FLRHW/Strobe_main/HTML/images/cat_pdf_drill_map_Strobe_main-NPTH_drill_map.png

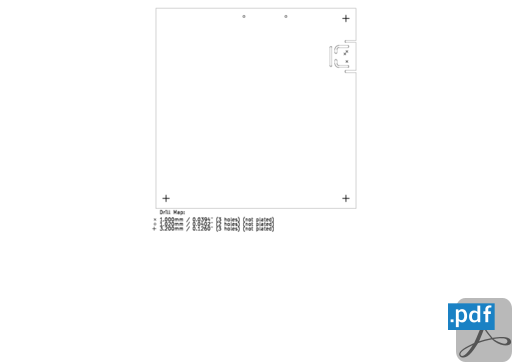
HTML/images/cat_pdf_drill_map_Strobe_main-NPTH_drill_map.png
