FLRHW/Strobe_main/HTML/images/cat_png_3d_viewer_bottom_Strobe_main-bottom.png

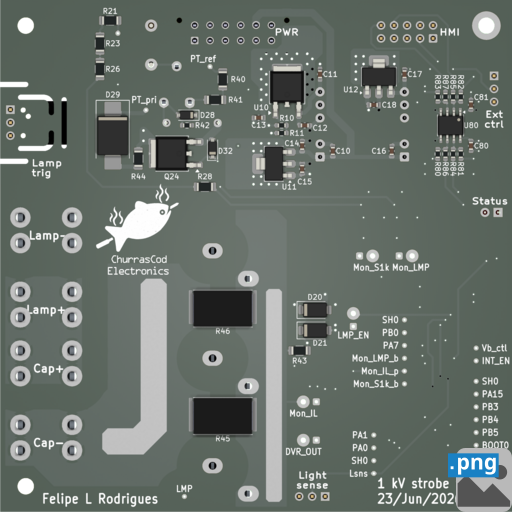
HTML/images/cat_png_3d_viewer_bottom_Strobe_main-bottom.png
