FLRHW/Strobe_main/HTML/images/cat_png_3d_viewer_top_Strobe_main-top.png

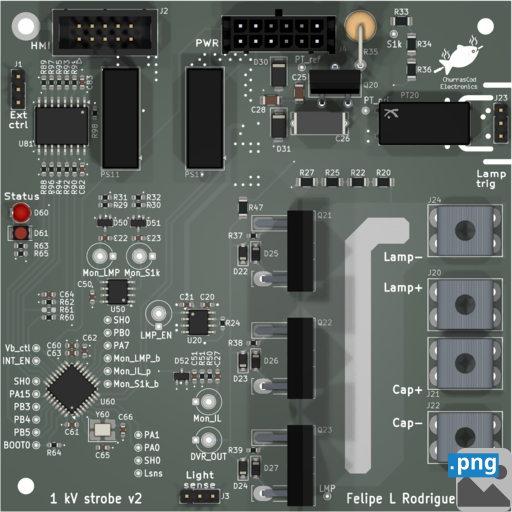
HTML/images/cat_png_3d_viewer_top_Strobe_main-top.png
