FLRHW/Strobe_main/Images/bot.jpg

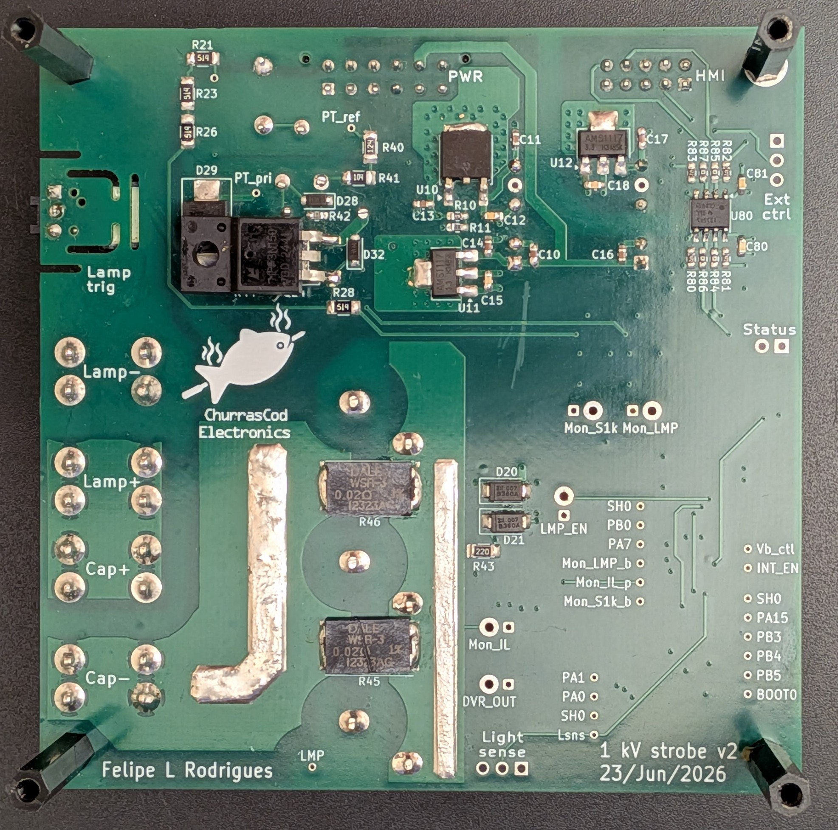
Images/bot.jpg
