FLRHW/Strobe_main/Manufacturing/Fabrication/Strobe_main-fabrication.pdf

# Top Fabrication (Scale 1:1) Main board Fabrication Document

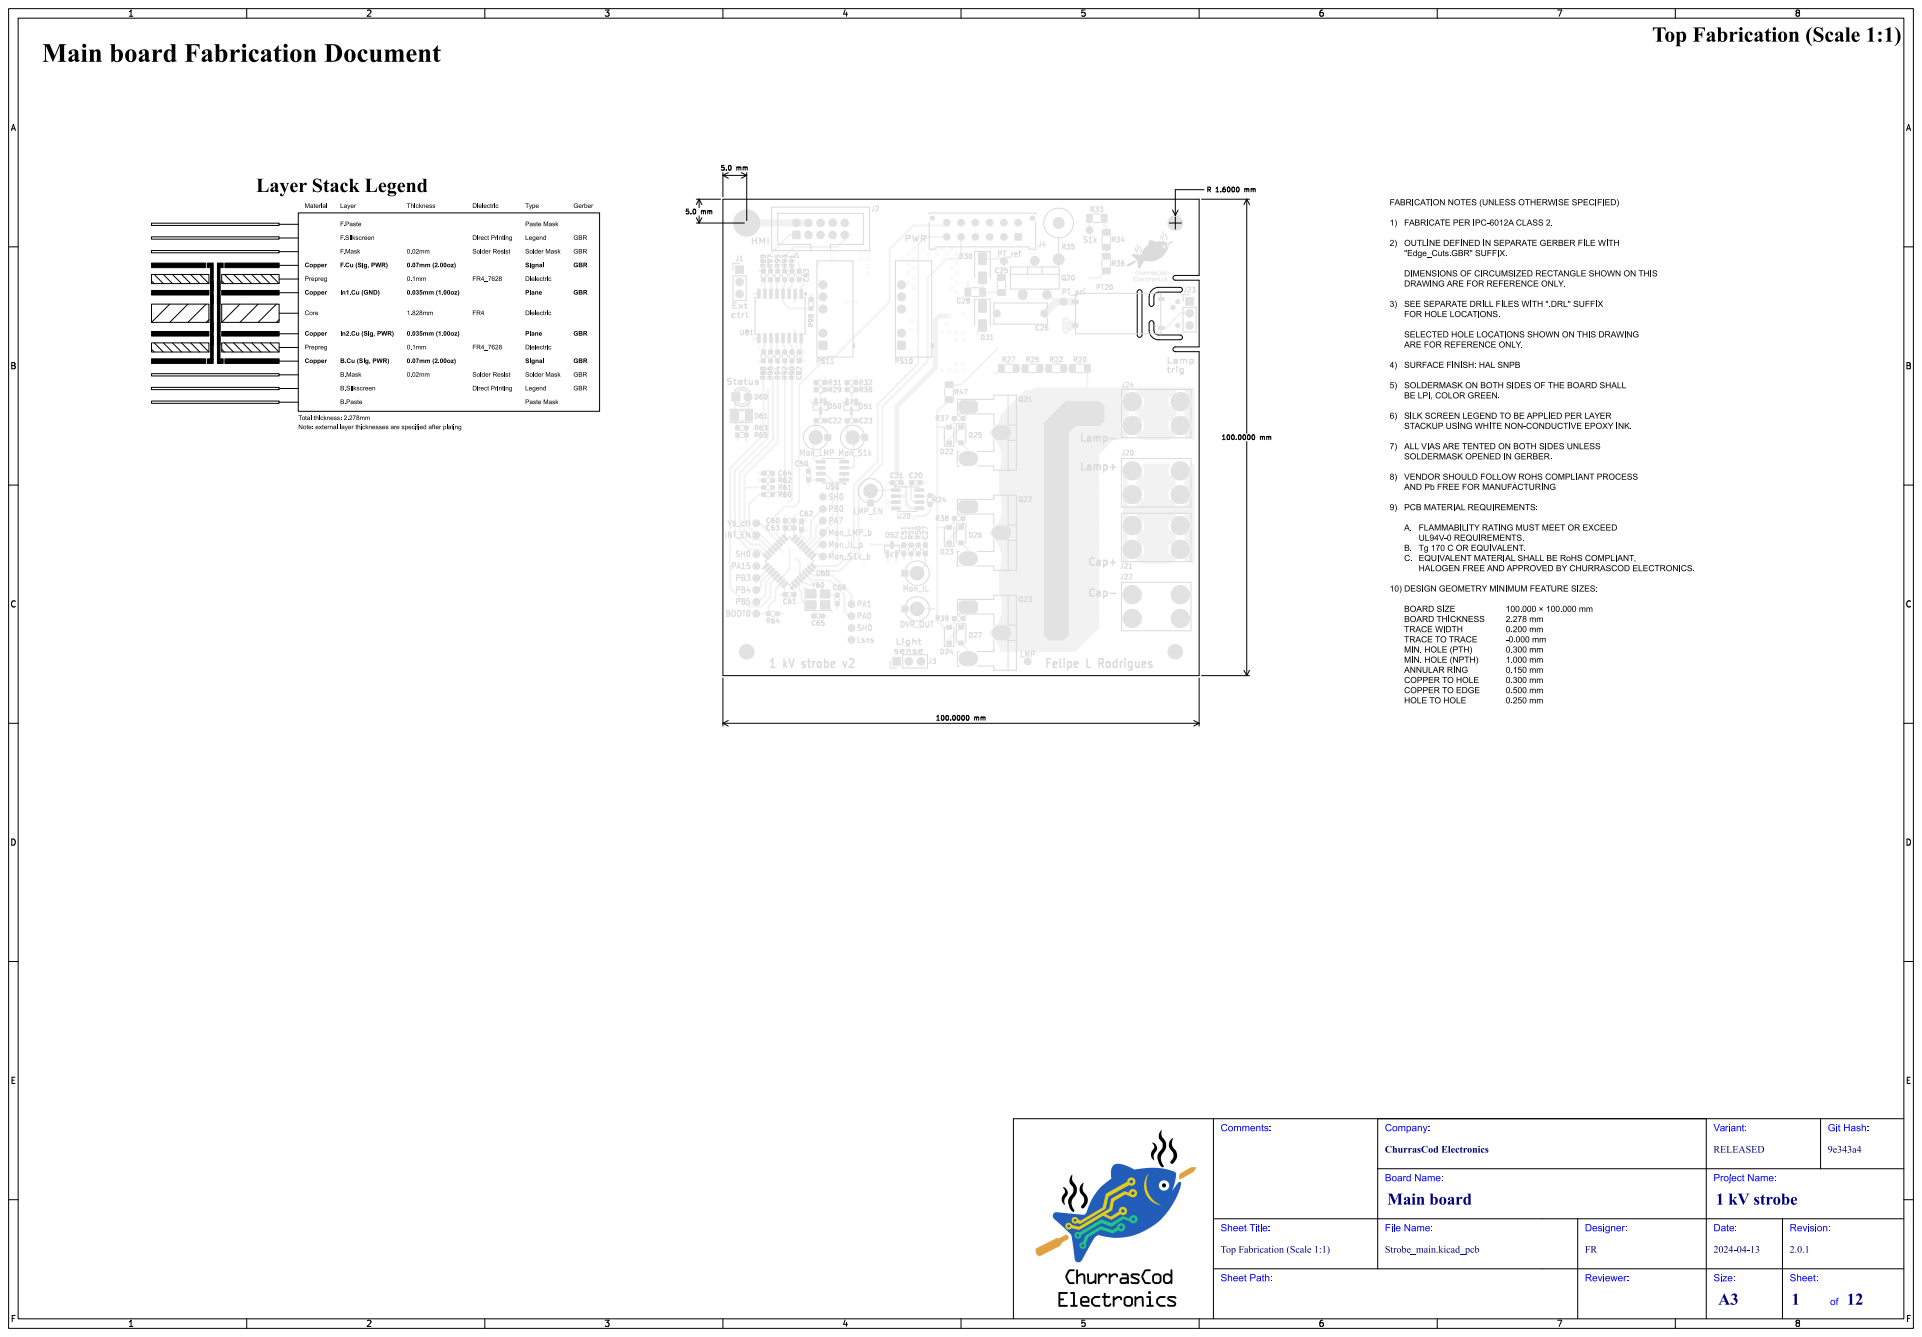
[picture p12: page 1]

# Bottom Fabrication (Scale 1:1) Main board Fabrication Document

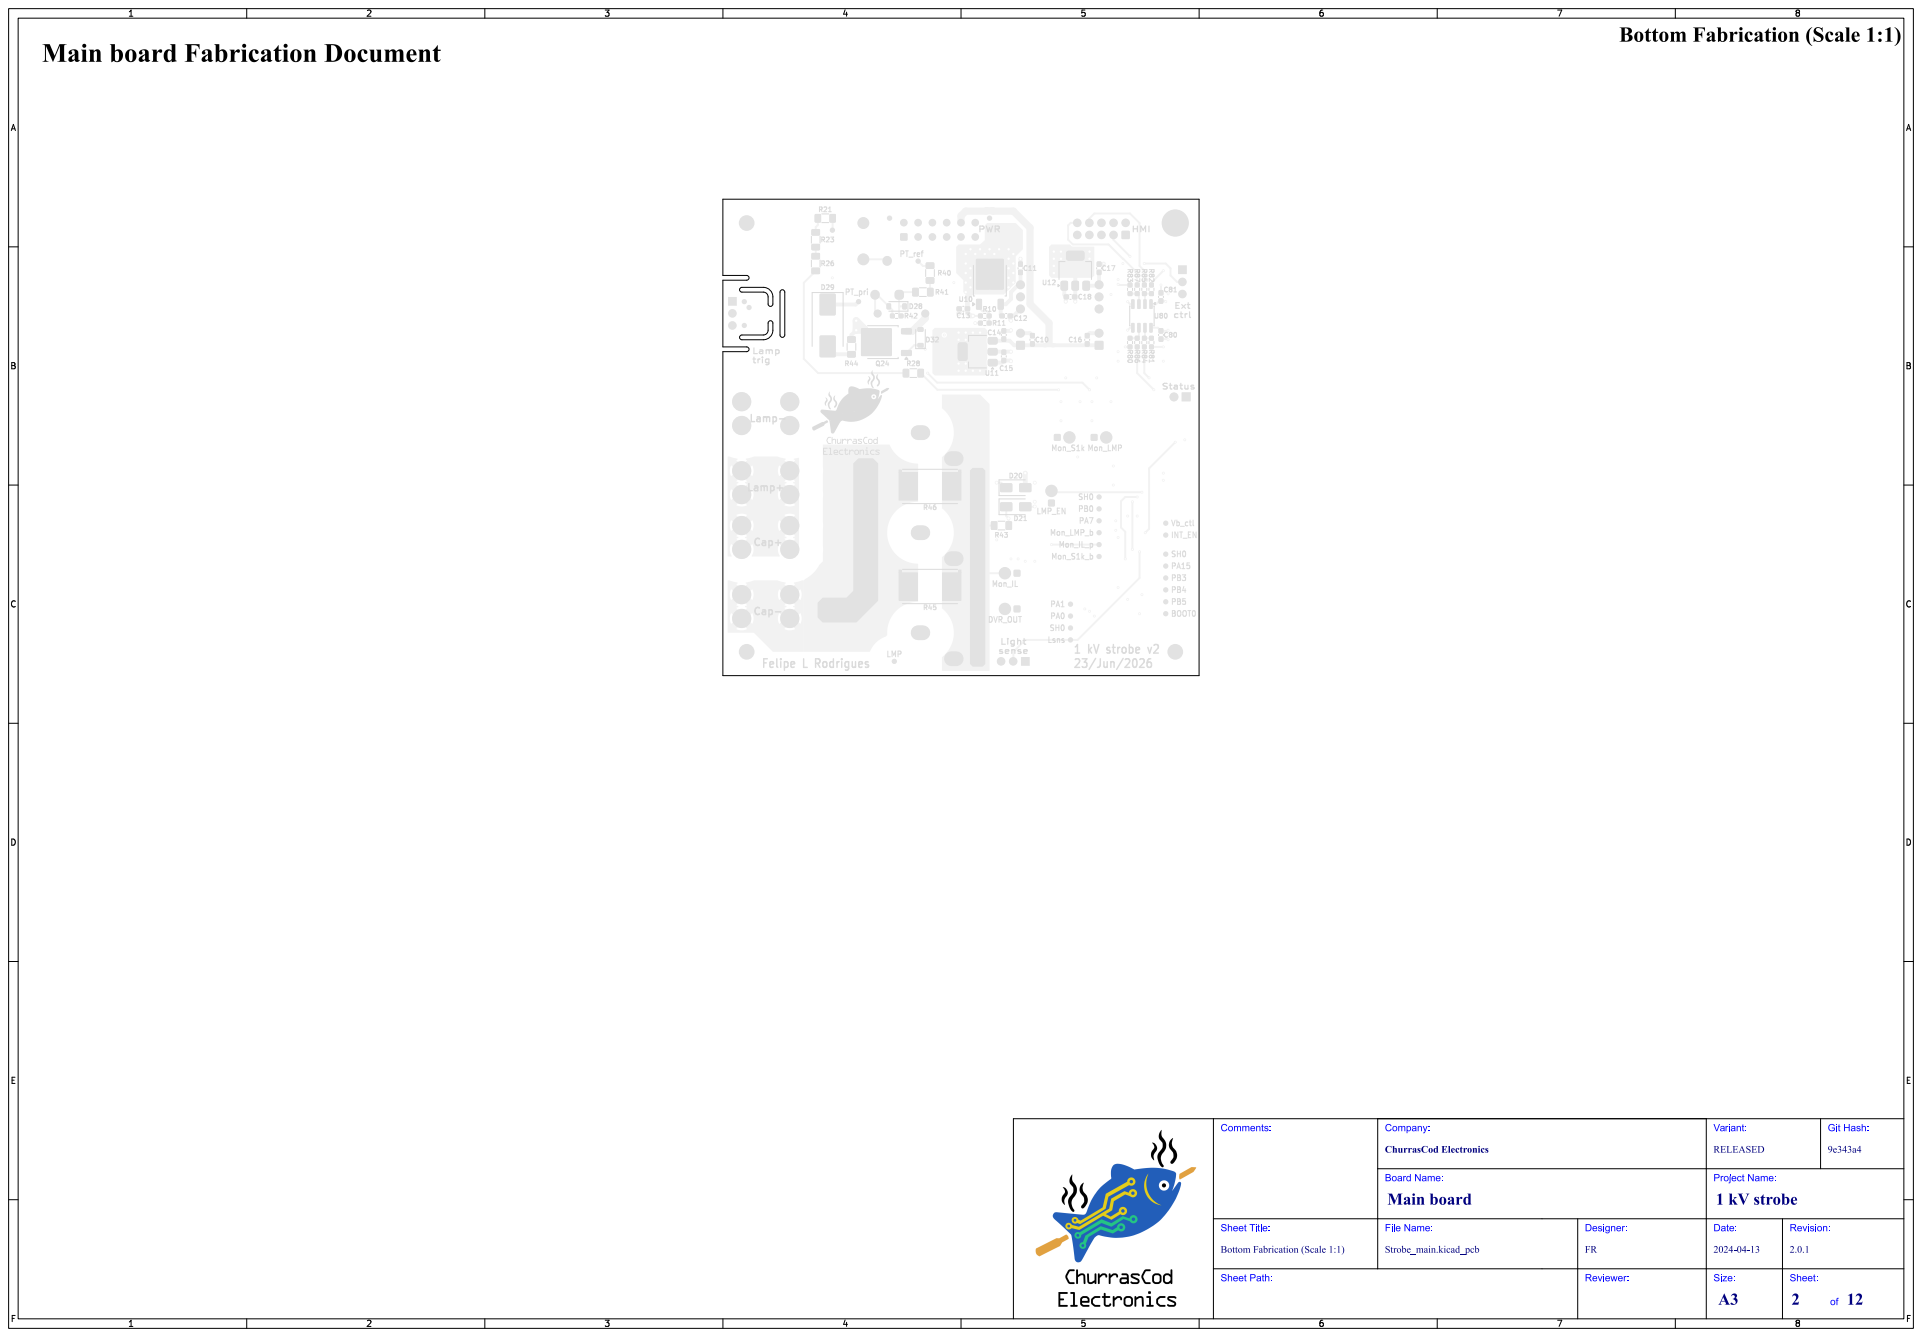
[picture p13: page 2]

# Drill Drawing L1 - L4 (Scale 1:1) Main board Fabrication Document

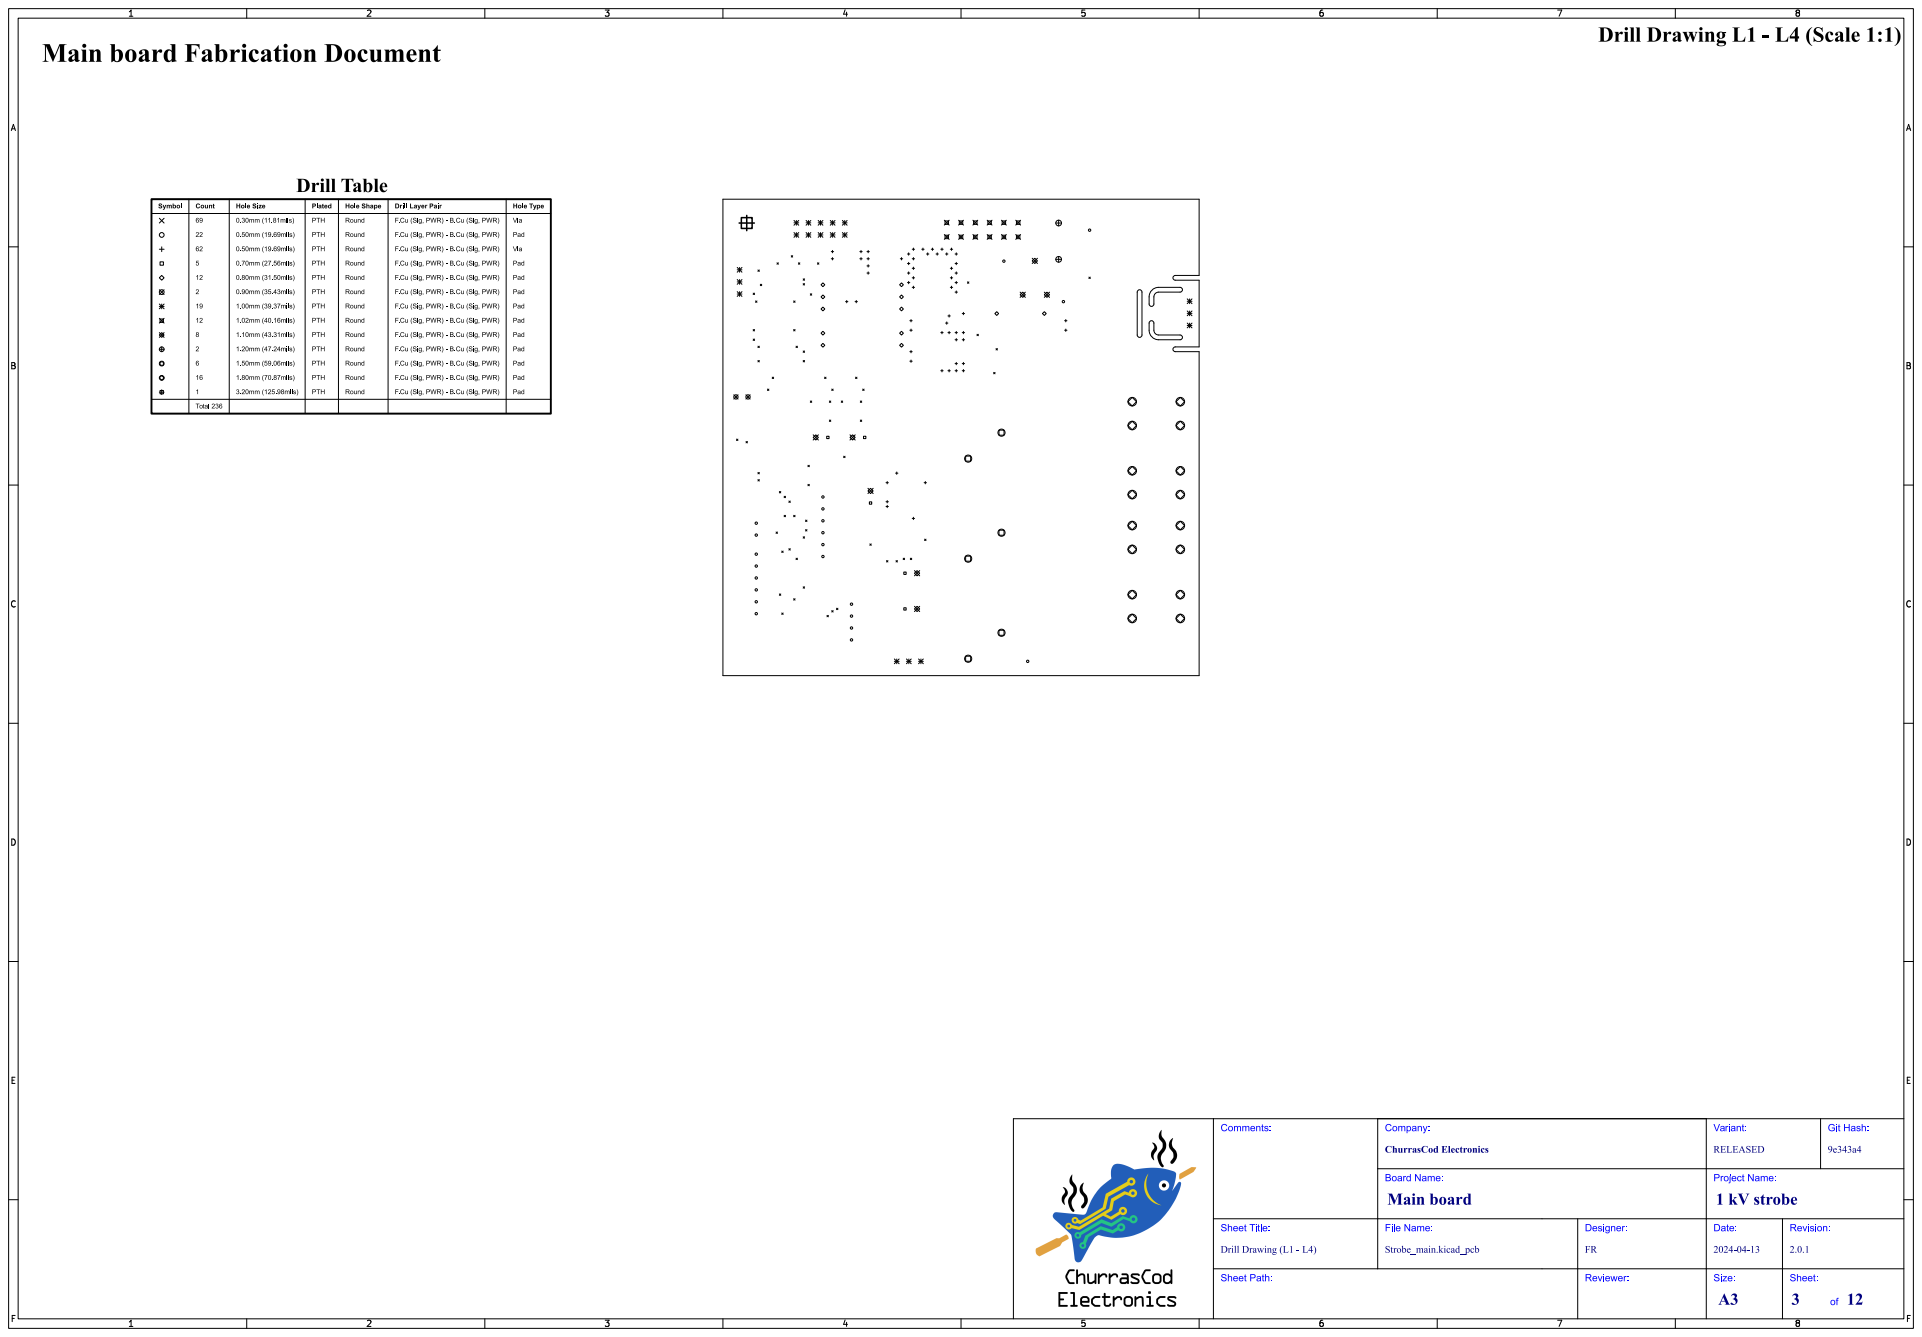
[picture p14: page 3]
Git; Hash:; Comments:; Drill Drawing (L1 - L4); Sheet Title:; File Name:; Main board; 1 kV strobe; ChurrasCod Electronics; Company:; RELEASED; Variant:; Board Name:; Strobe_main.kicad_pcb; Designer:; Project Name:; Date:; Revision:

# Drill Drawing L1 - L4 (Scale 1:1) Main board Fabrication Document

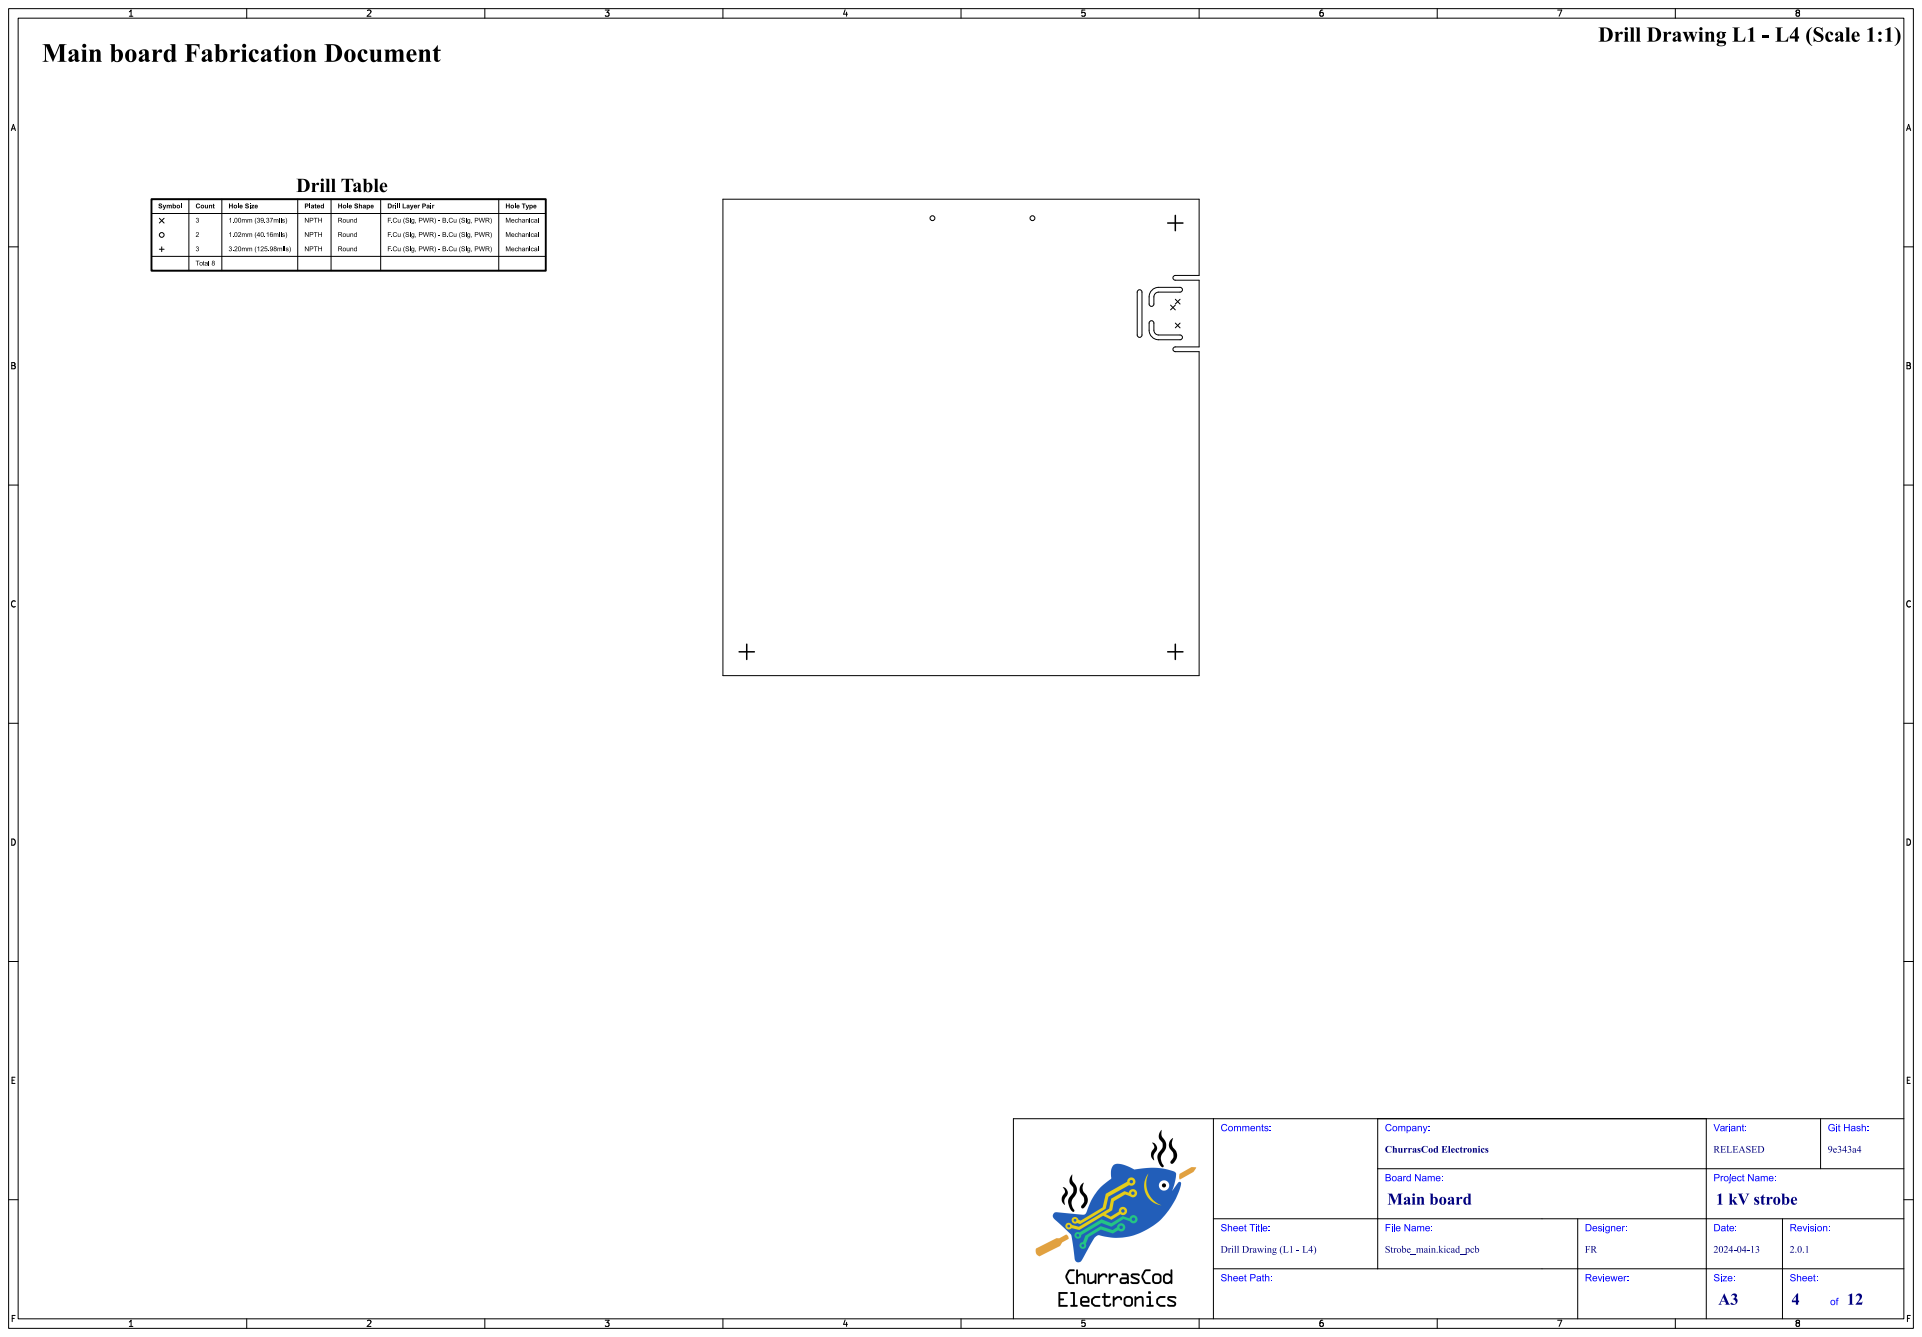
[picture p15: page 4]
Git; Hash:; Comments:; Drill Drawing (L1 - L4); Sheet Title:; File Name:; Main board; 1 kV strobe; ChurrasCod Electronics; Company:; RELEASED; Variant:; Board Name:; Strobe_main.kicad_pcb; Designer:; Project Name:; Date:; Revision:

# F.Cu (Sig, PWR) (Scale 1:1) Main board Fabrication Document

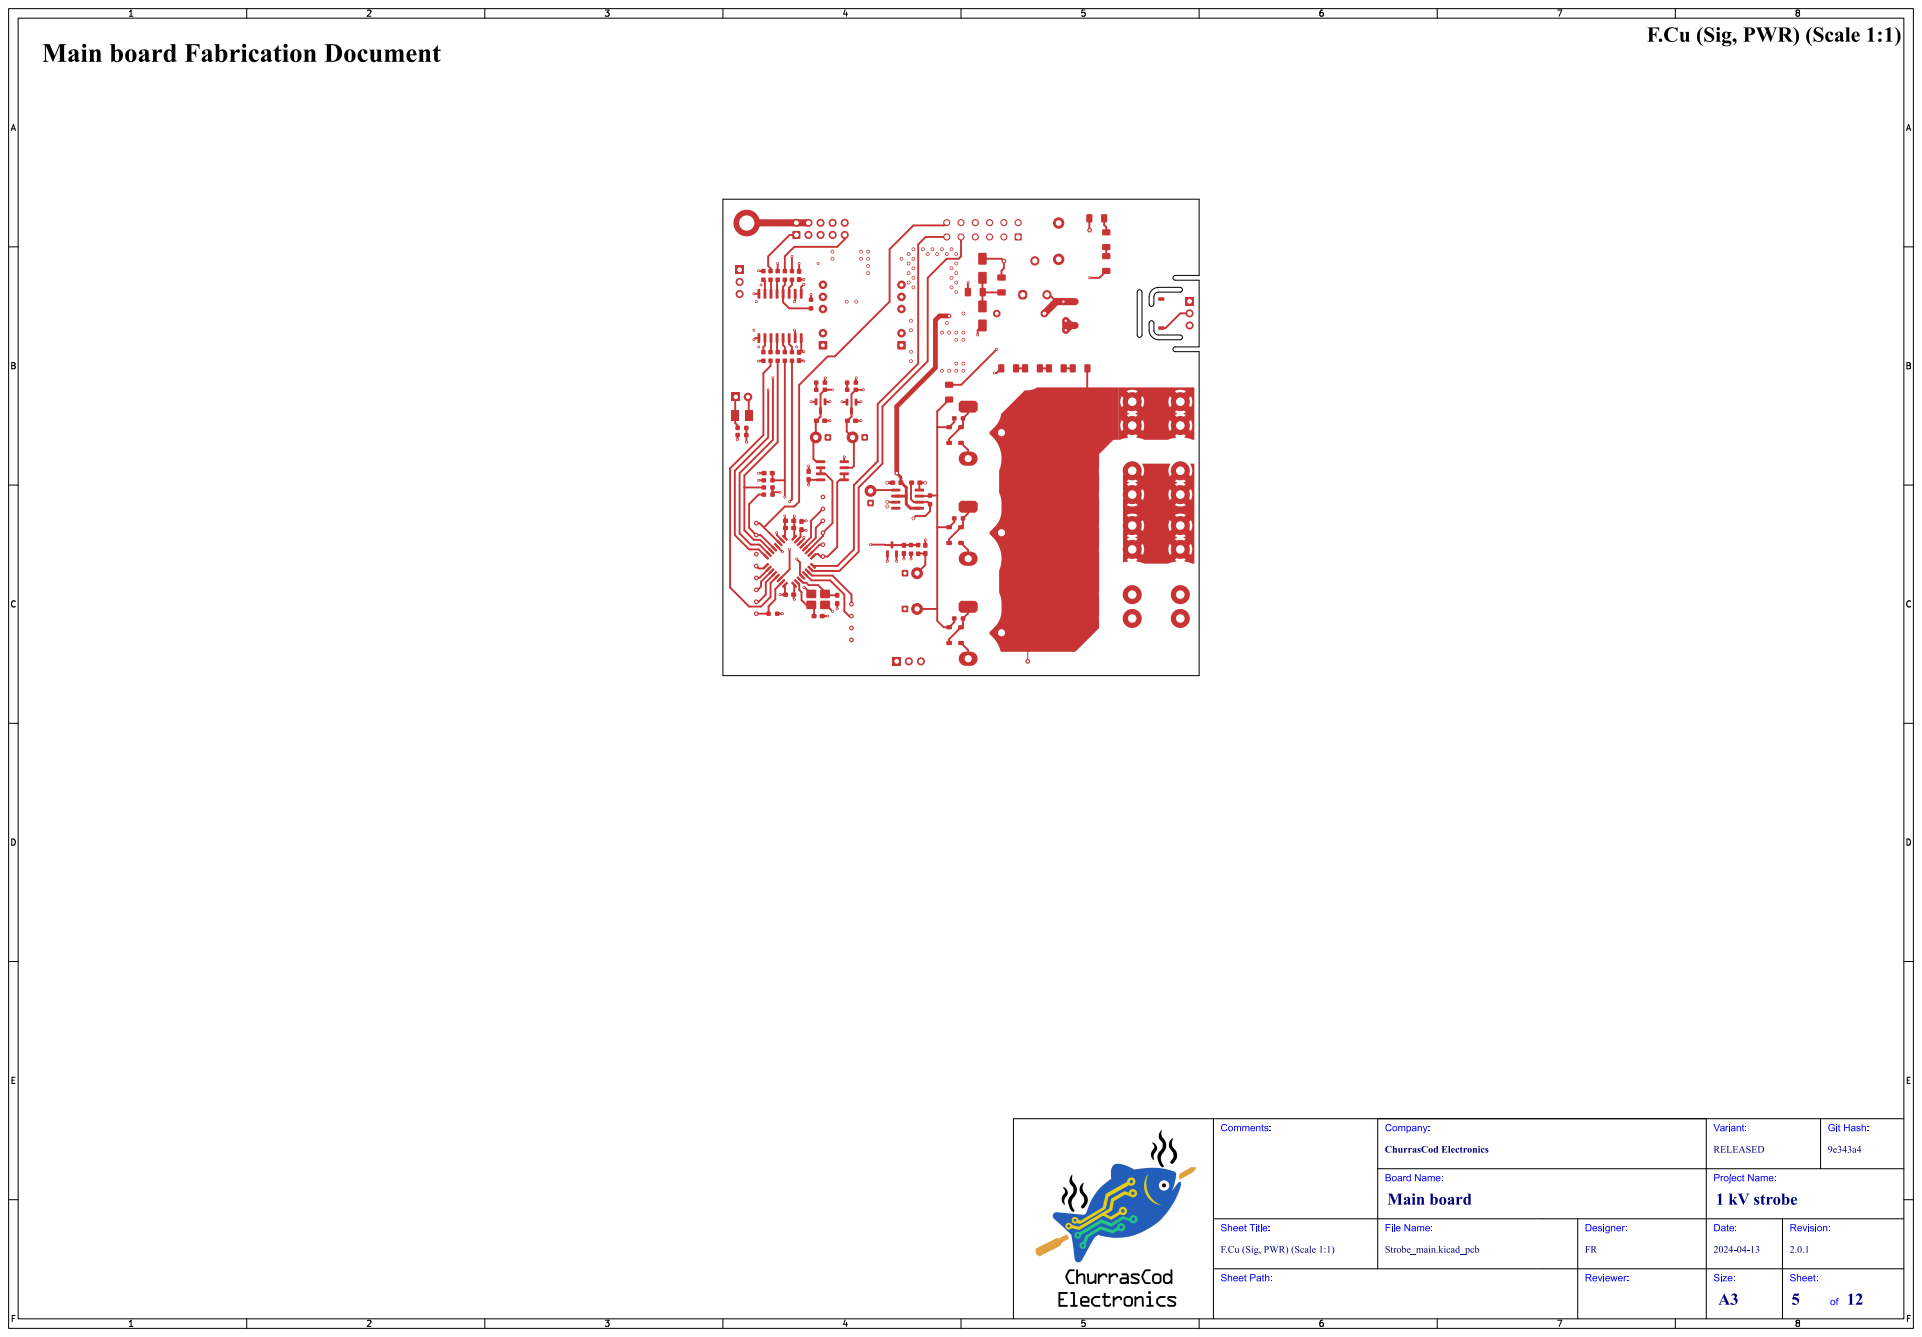
[picture p16: page 5]
Git; Hash:; Comments:; Sheet Title:; File Name:; Main board; 1 kV strobe; ChurrasCod Electronics; Company:; RELEASED; Variant:; Board Name:; Strobe_main.kicad_pcb; Designer:; Project Name:; Date:; Revision:

F.Cu (Sig, PWR) (Scale 1:1)

# In1.Cu (GND) (Scale 1:1) Main board Fabrication Document

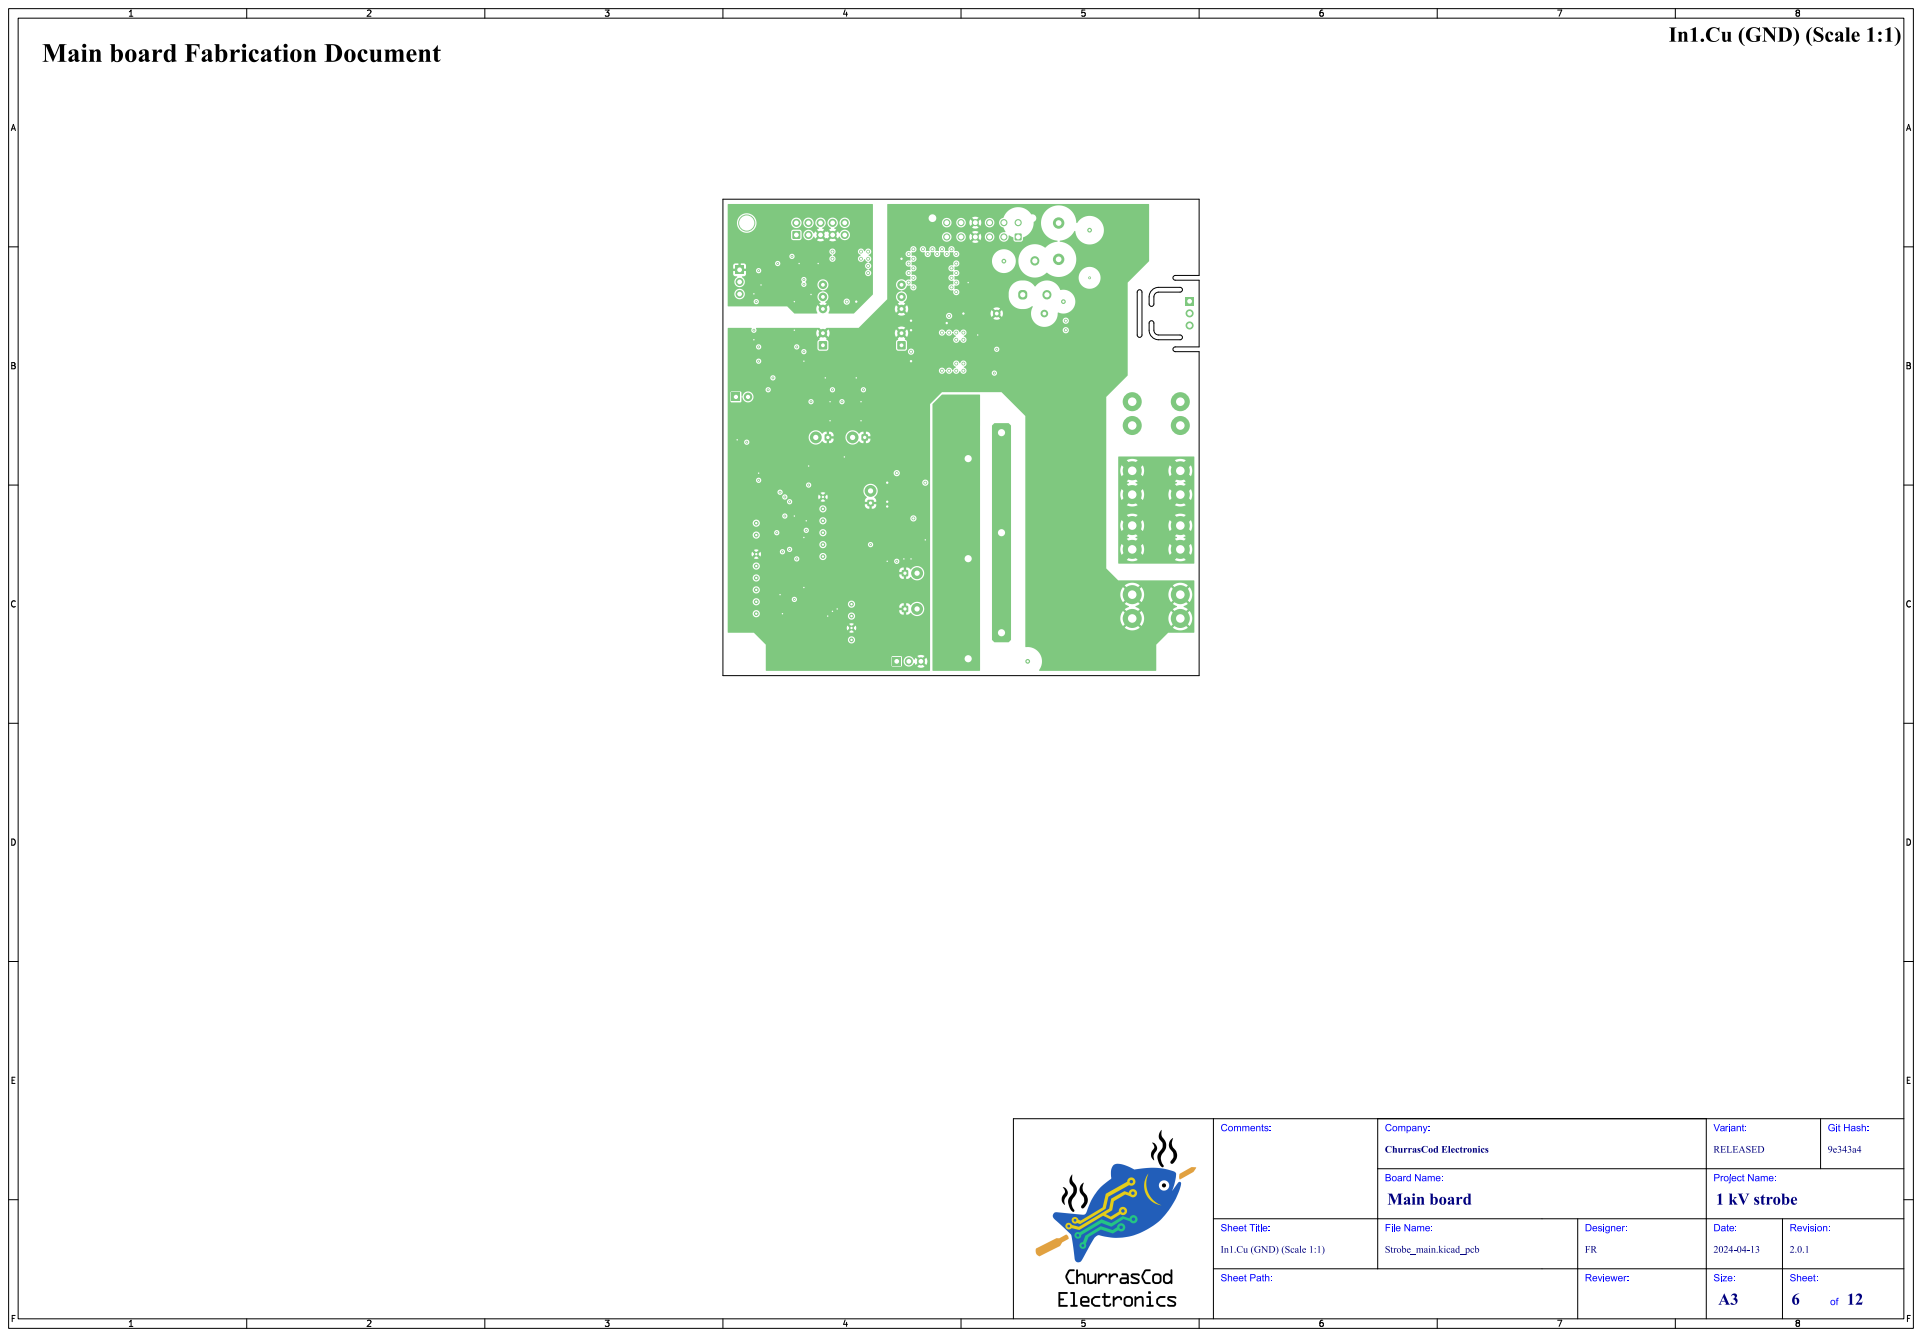
[picture p17: page 6]
Git; Hash:; Comments:; Sheet Title:; File Name:; Main board; 1 kV strobe; ChurrasCod Electronics; Company:; RELEASED; Variant:; Board Name:; Strobe_main.kicad_pcb; Designer:; Project Name:; Date:; Revision:

In1.Cu (GND) (Scale 1:1)

# In2.Cu (Sig, PWR) (Scale 1:1) Main board Fabrication Document

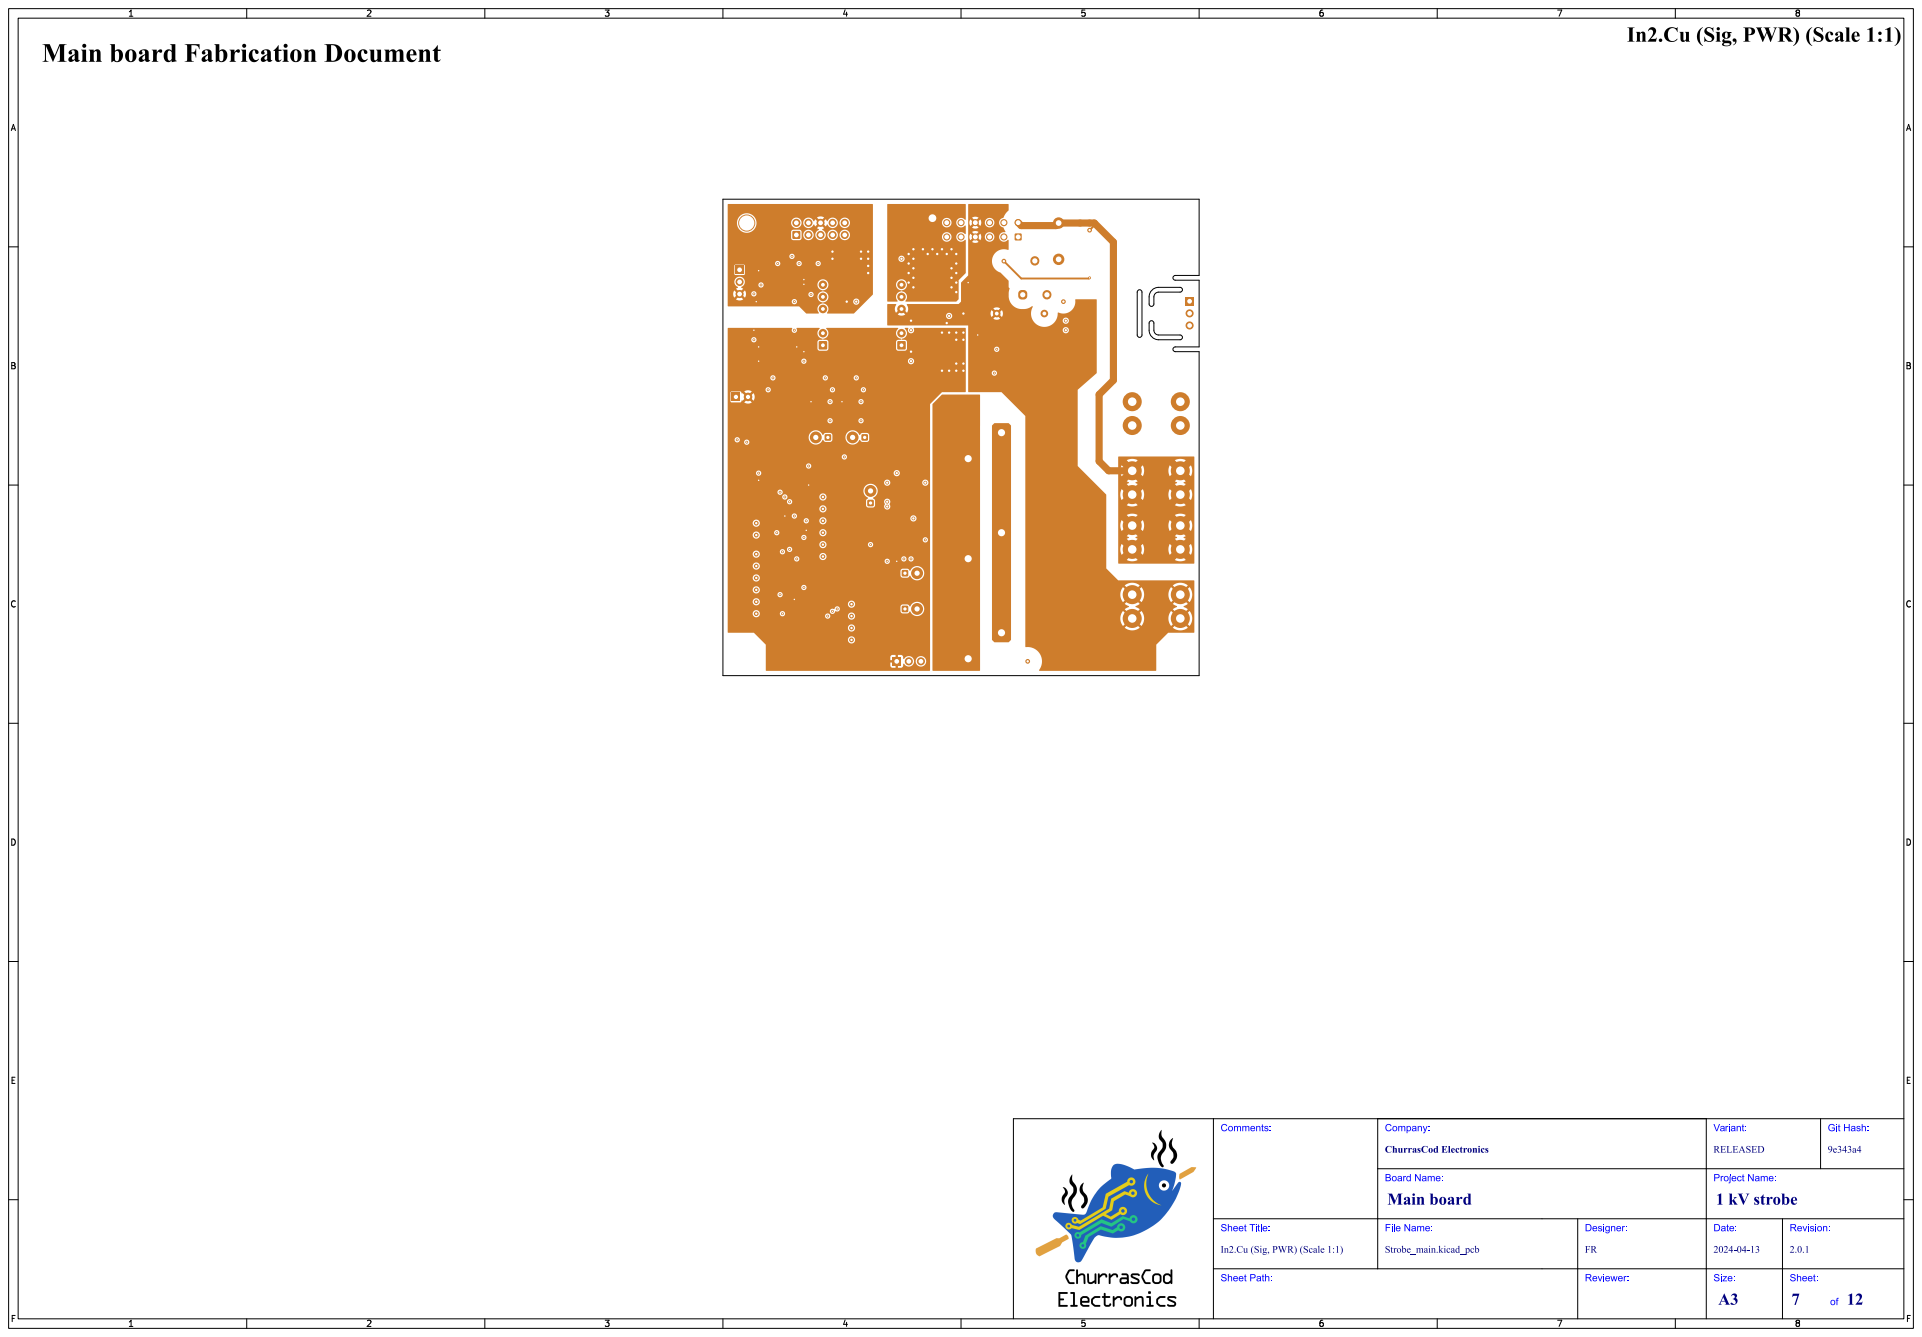
[picture p18: page 7]
Git; Hash:; Comments:; Sheet Title:; File Name:; Main board; 1 kV strobe; ChurrasCod Electronics; Company:; RELEASED; Variant:; Board Name:; Strobe_main.kicad_pcb; Designer:; Project Name:; Date:; Revision:

In2.Cu (Sig, PWR) (Scale 1:1)

# B.Cu (Sig, PWR) (Scale 1:1) Main board Fabrication Document

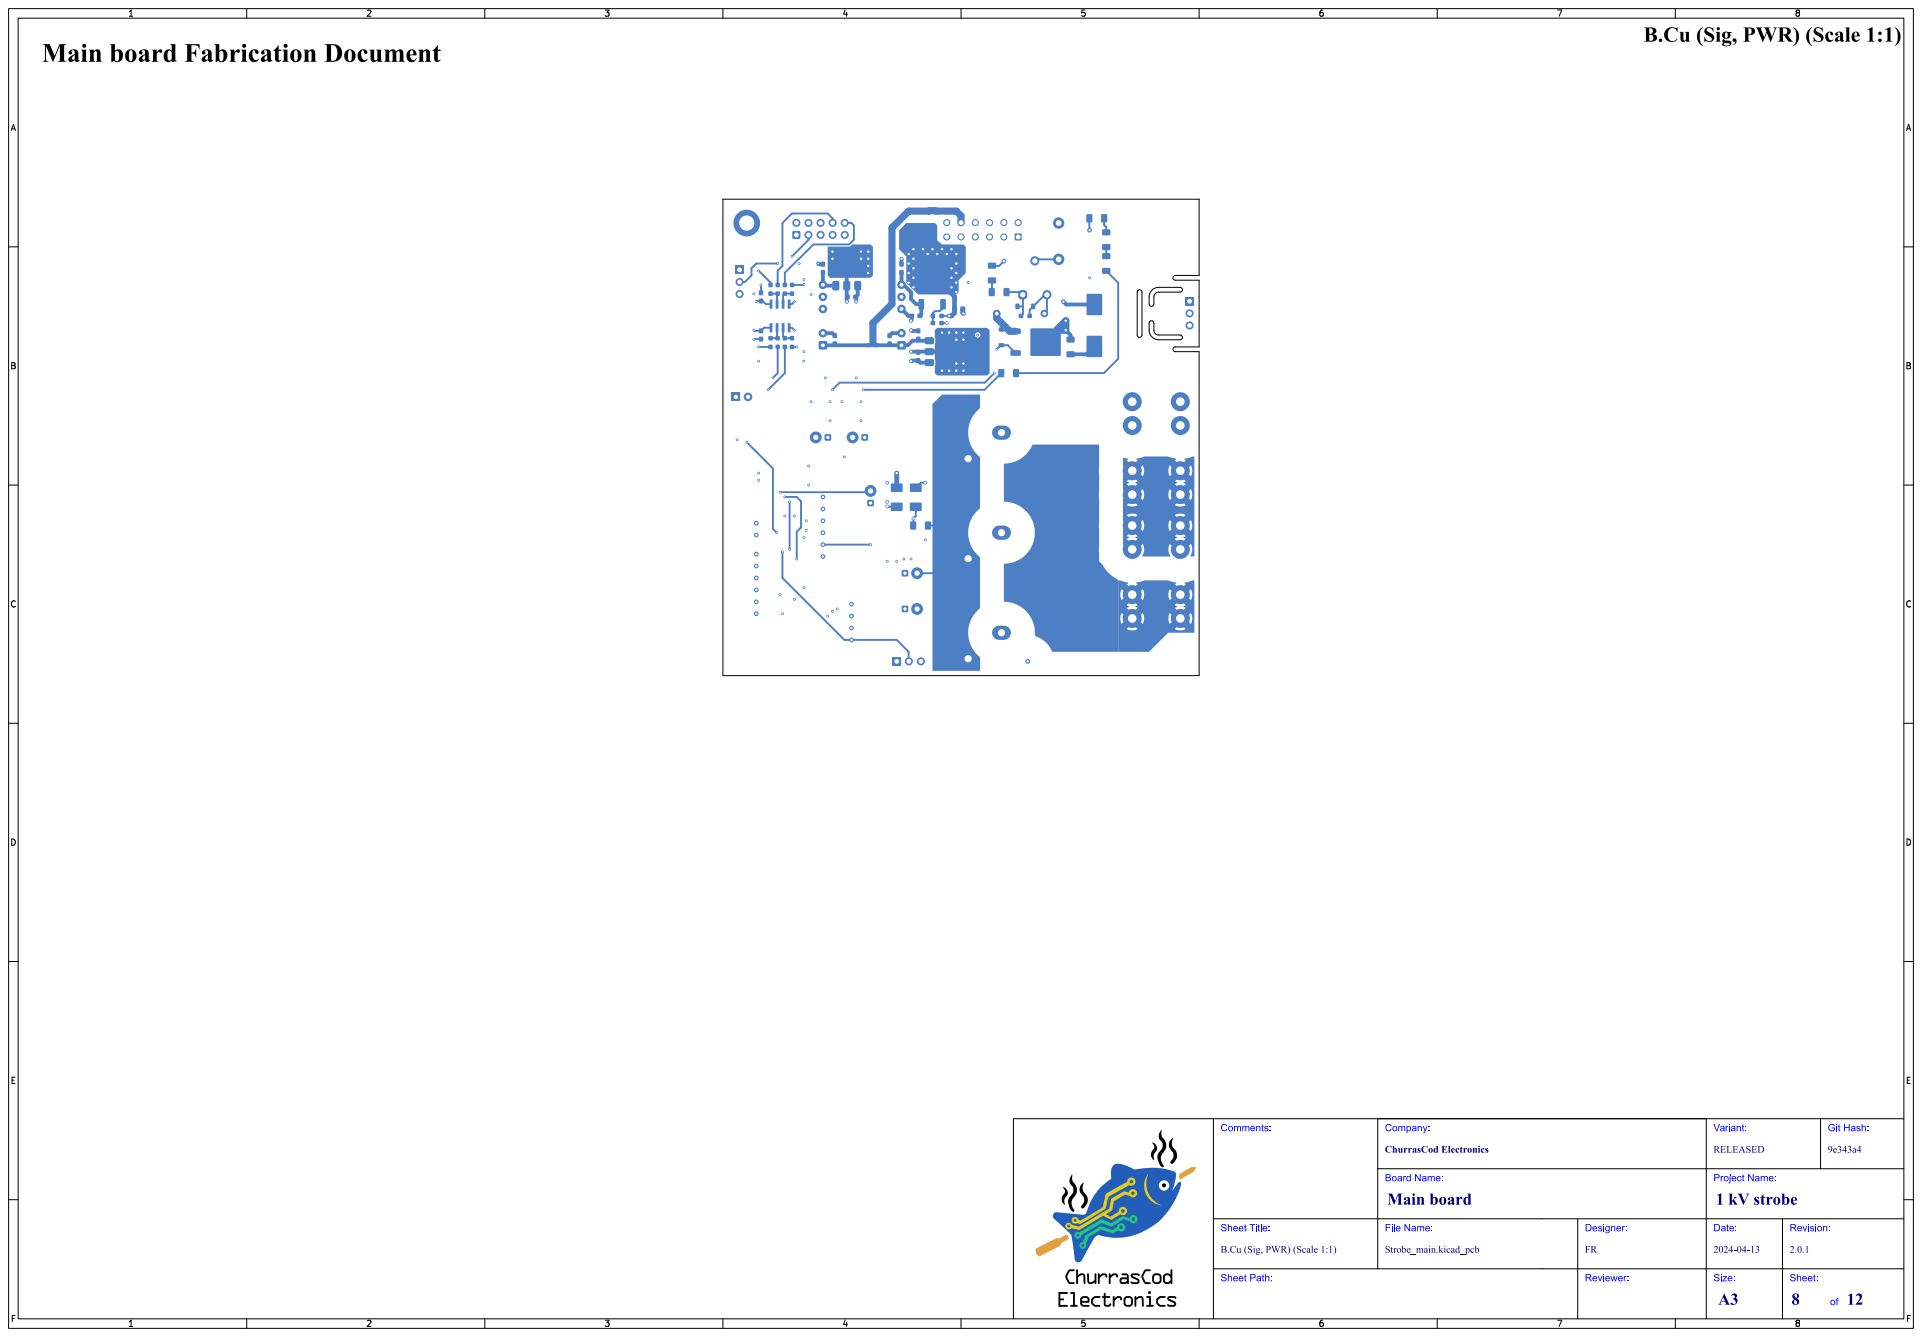
[picture p19: page 8]
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

B.Cu (Sig, PWR) (Scale 1:1)

# F.Mask (Scale 1:1) Main board Fabrication Document

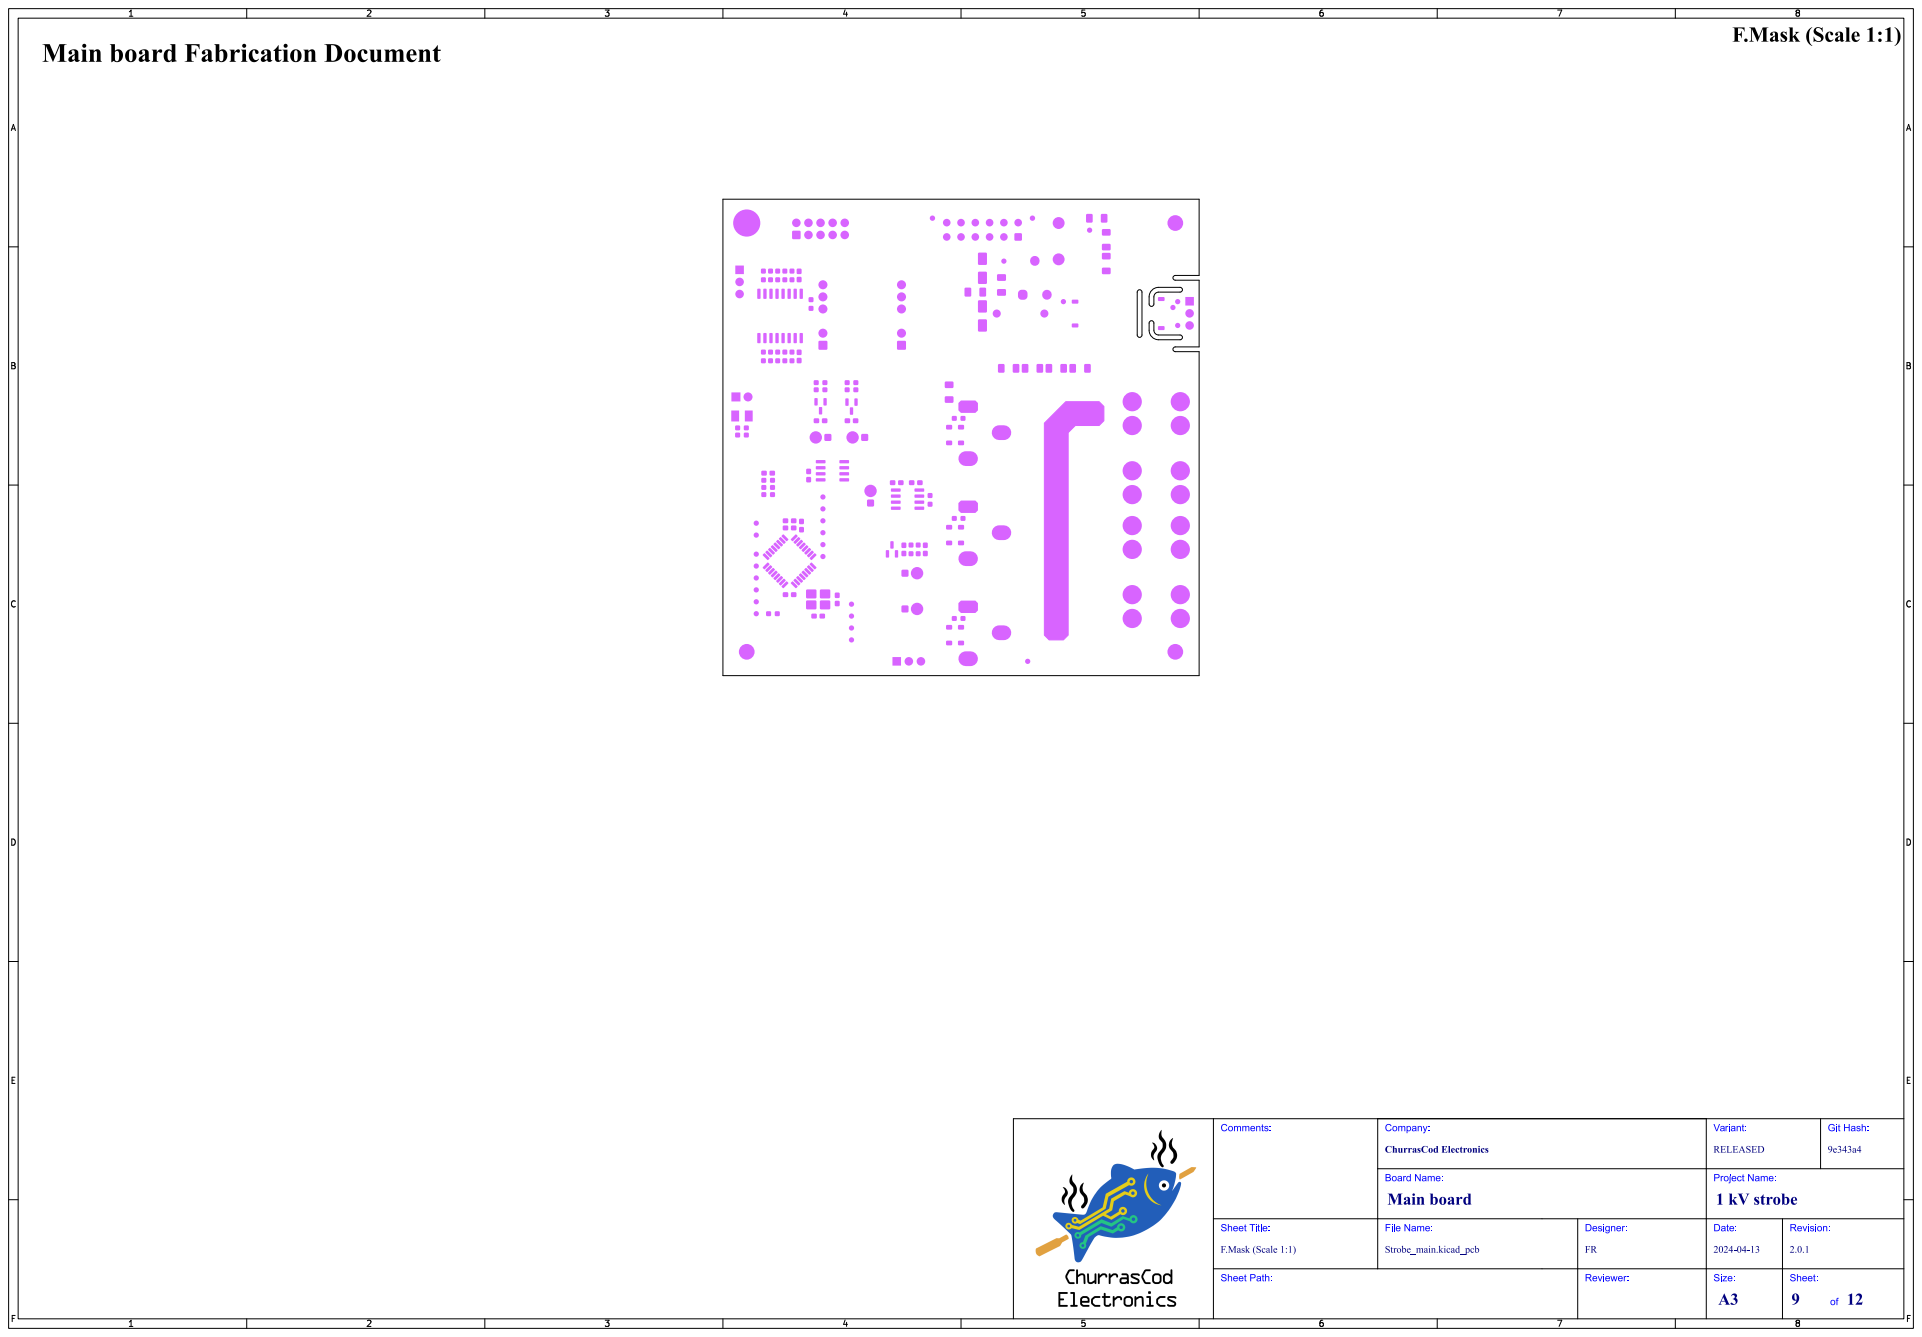
[picture p20: page 9]
Git; Hash:; Comments:; F.Mask (Scale 1:1); Sheet Title:; File Name:; Main board; 1 kV strobe; ChurrasCod Electronics; Company:; RELEASED; Variant:; Board Name:; Strobe_main.kicad_pcb; Designer:; Project Name:; Date:; Revision:

# B.Mask (Scale 1:1) Main board Fabrication Document

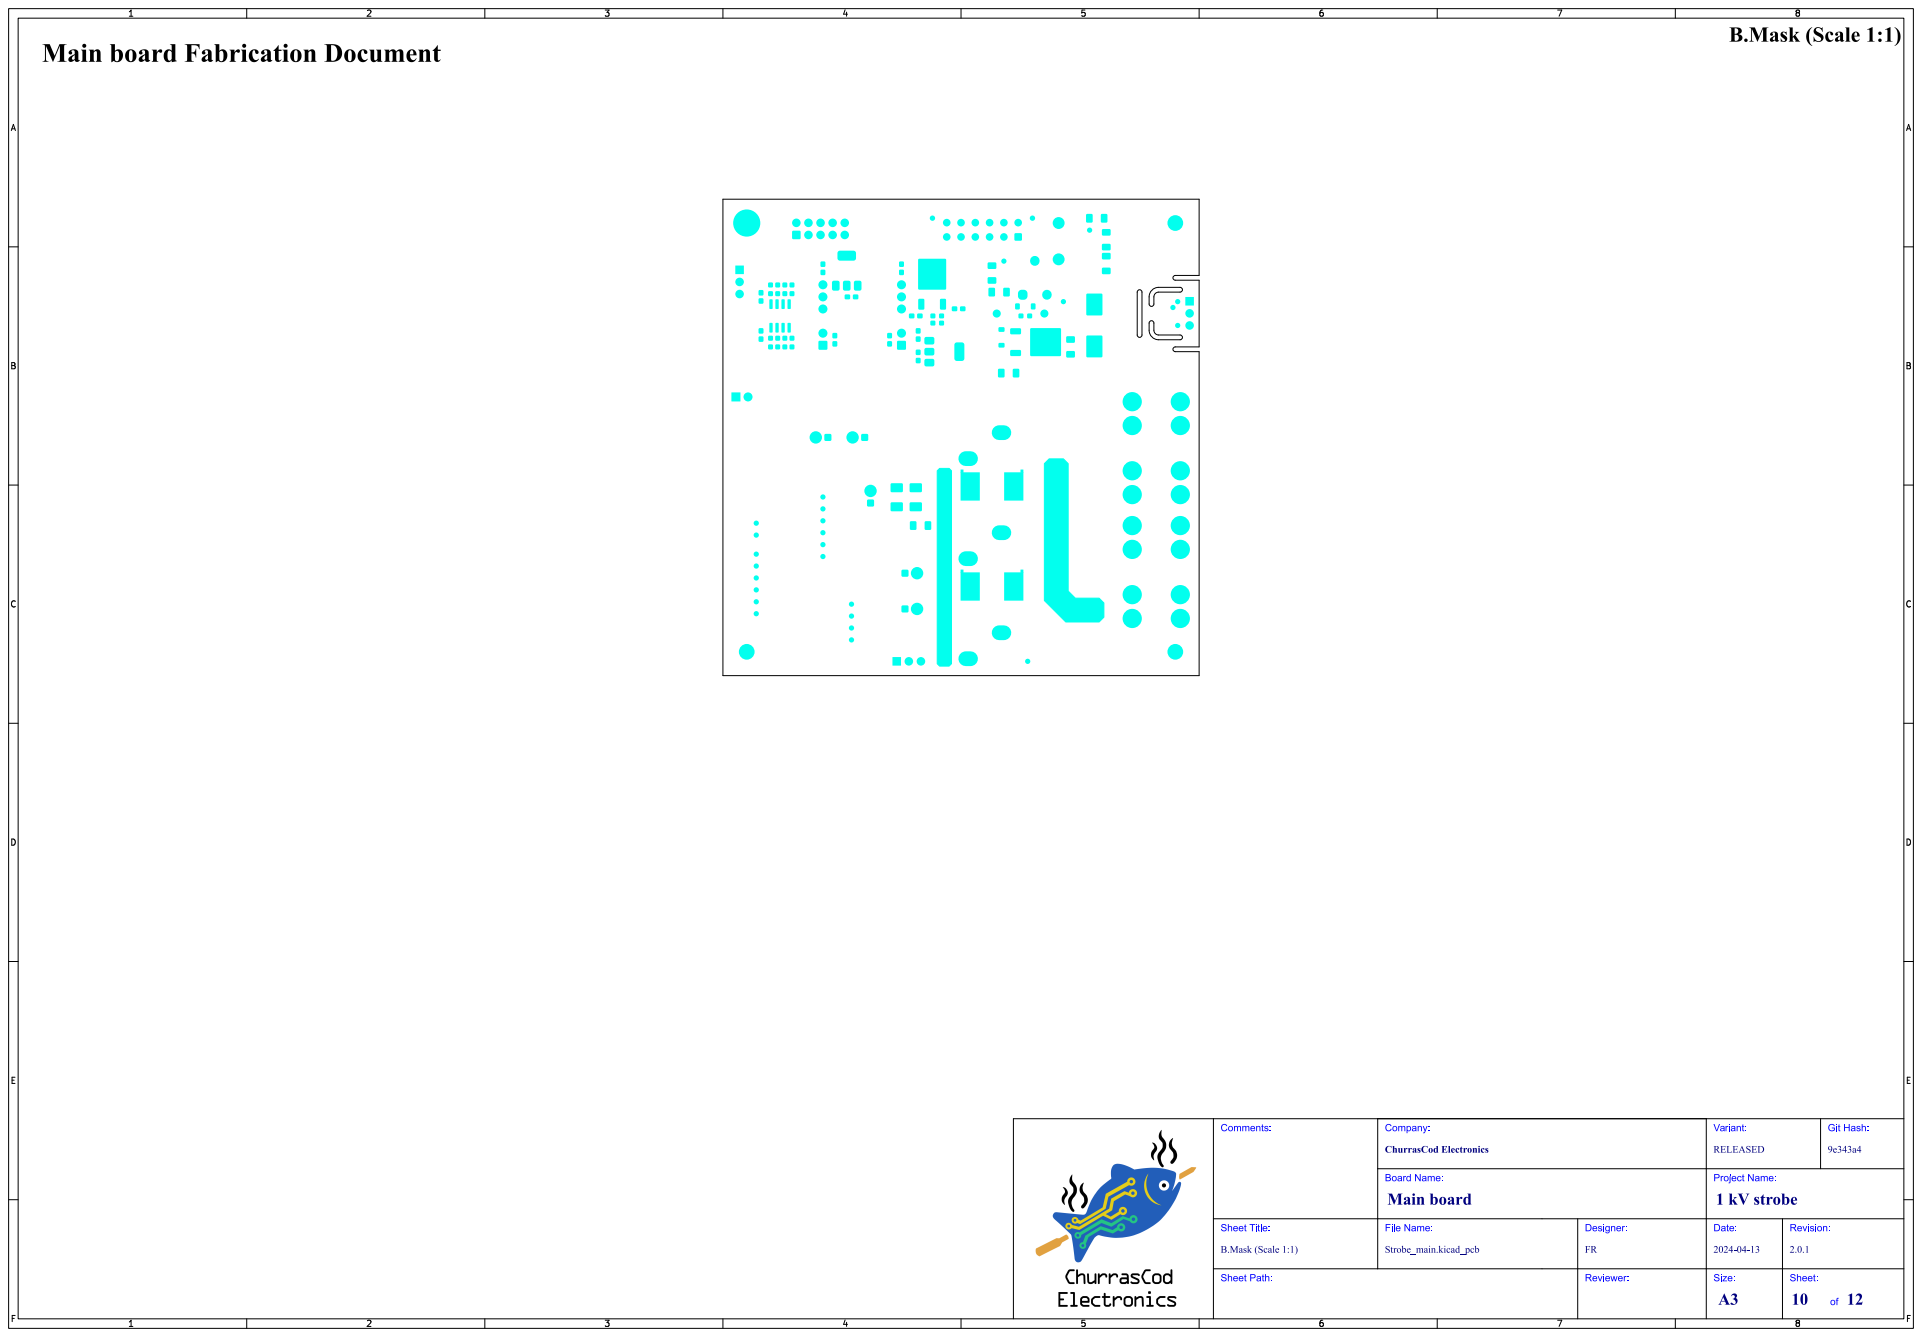
[picture p21: page 10]
Git; Hash:; Comments:; B.Mask (Scale 1:1); Sheet Title:; File Name:; Main board; 1 kV strobe; ChurrasCod Electronics; Company:; RELEASED; Variant:; Board Name:; Strobe_main.kicad_pcb; Designer:; Project Name:; Date:; Revision:

# F.Silkscreen (Scale 1:1) Main board Fabrication Document

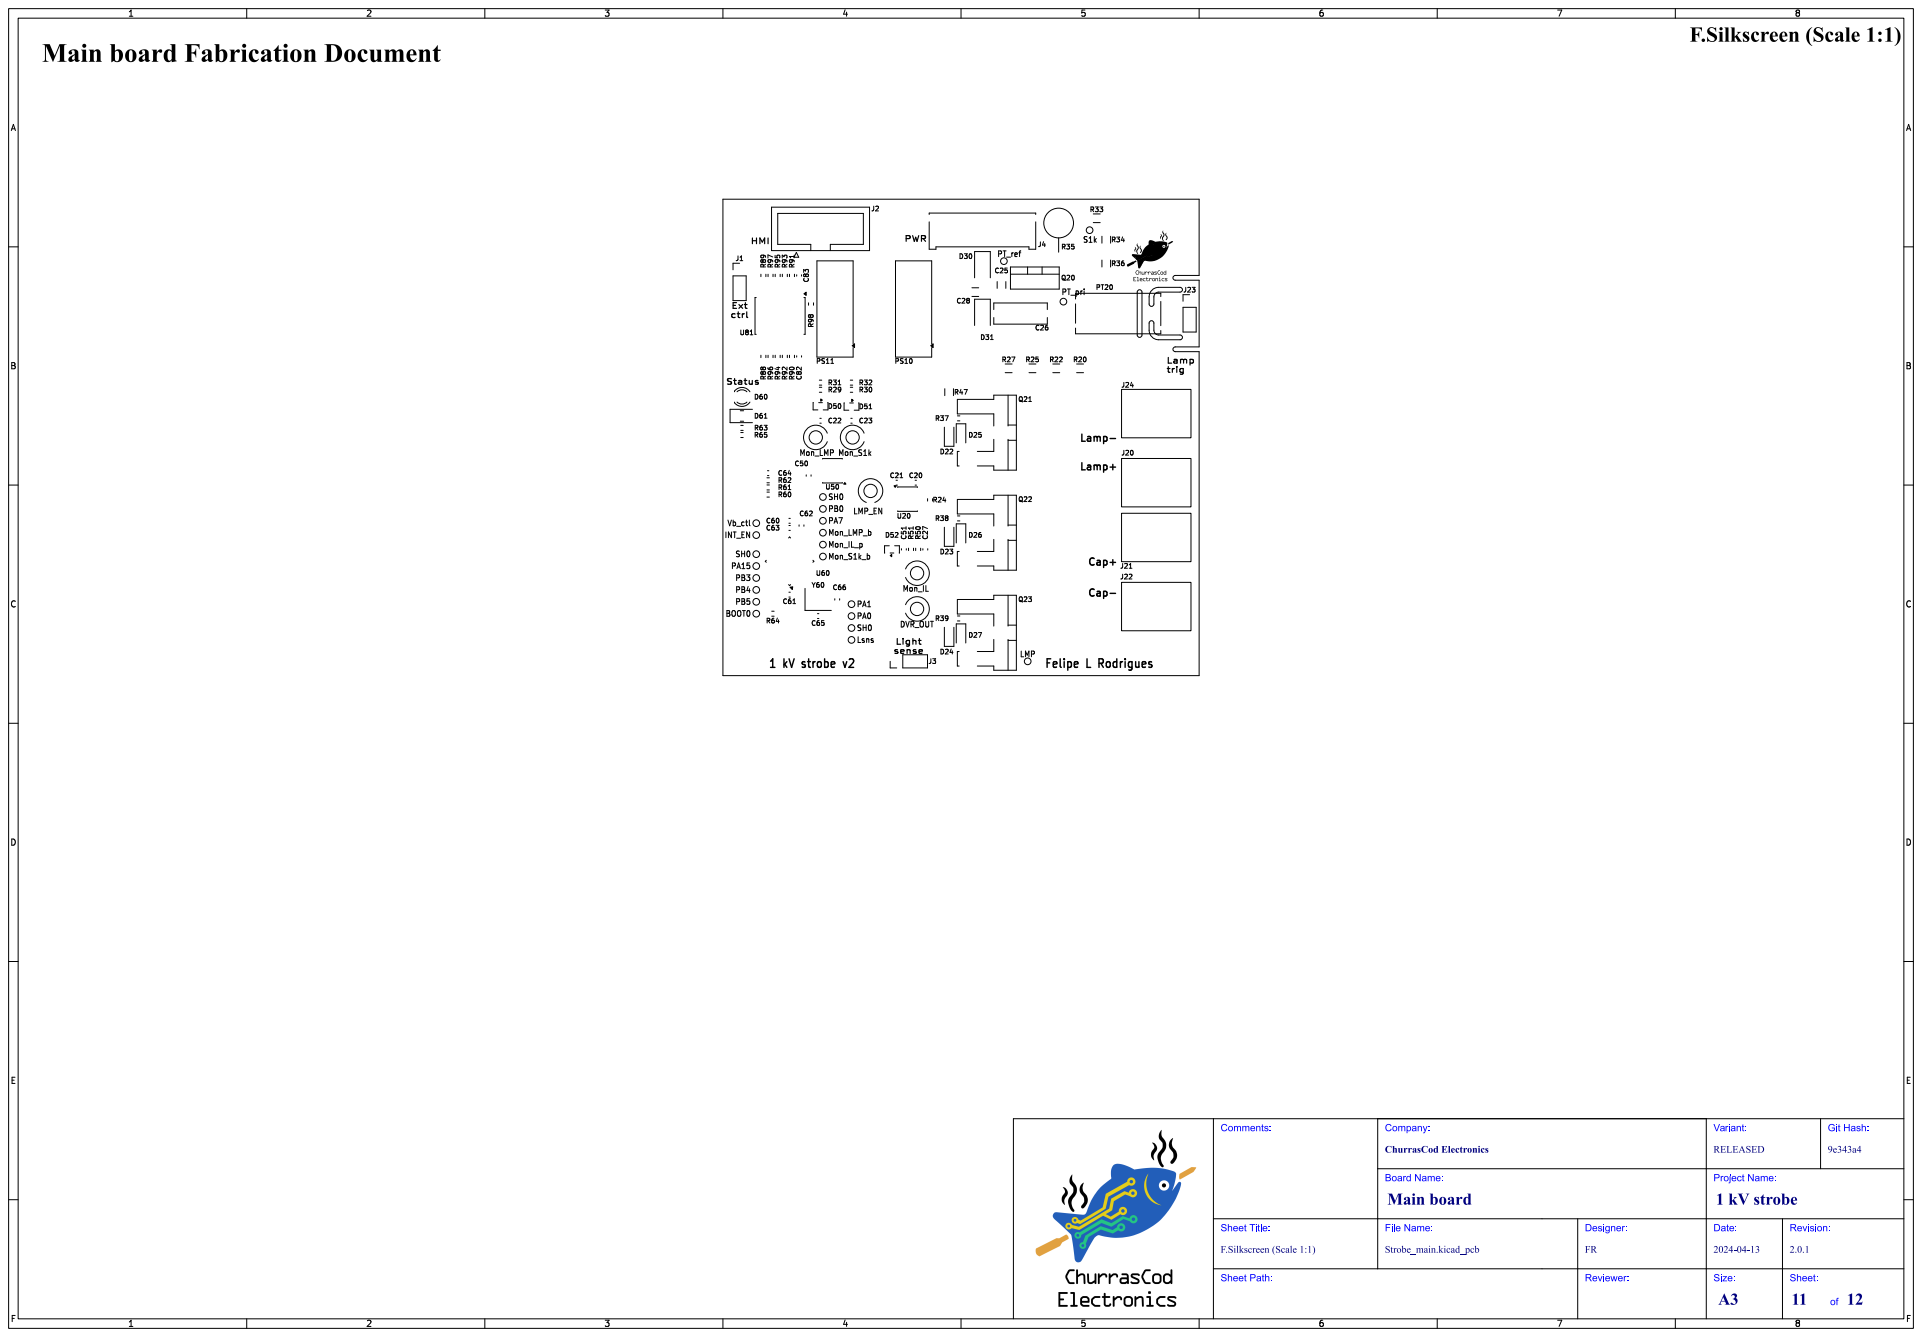
[picture p22: page 11]

# B.Silkscreen (Scale 1:1) Main board Fabrication Document

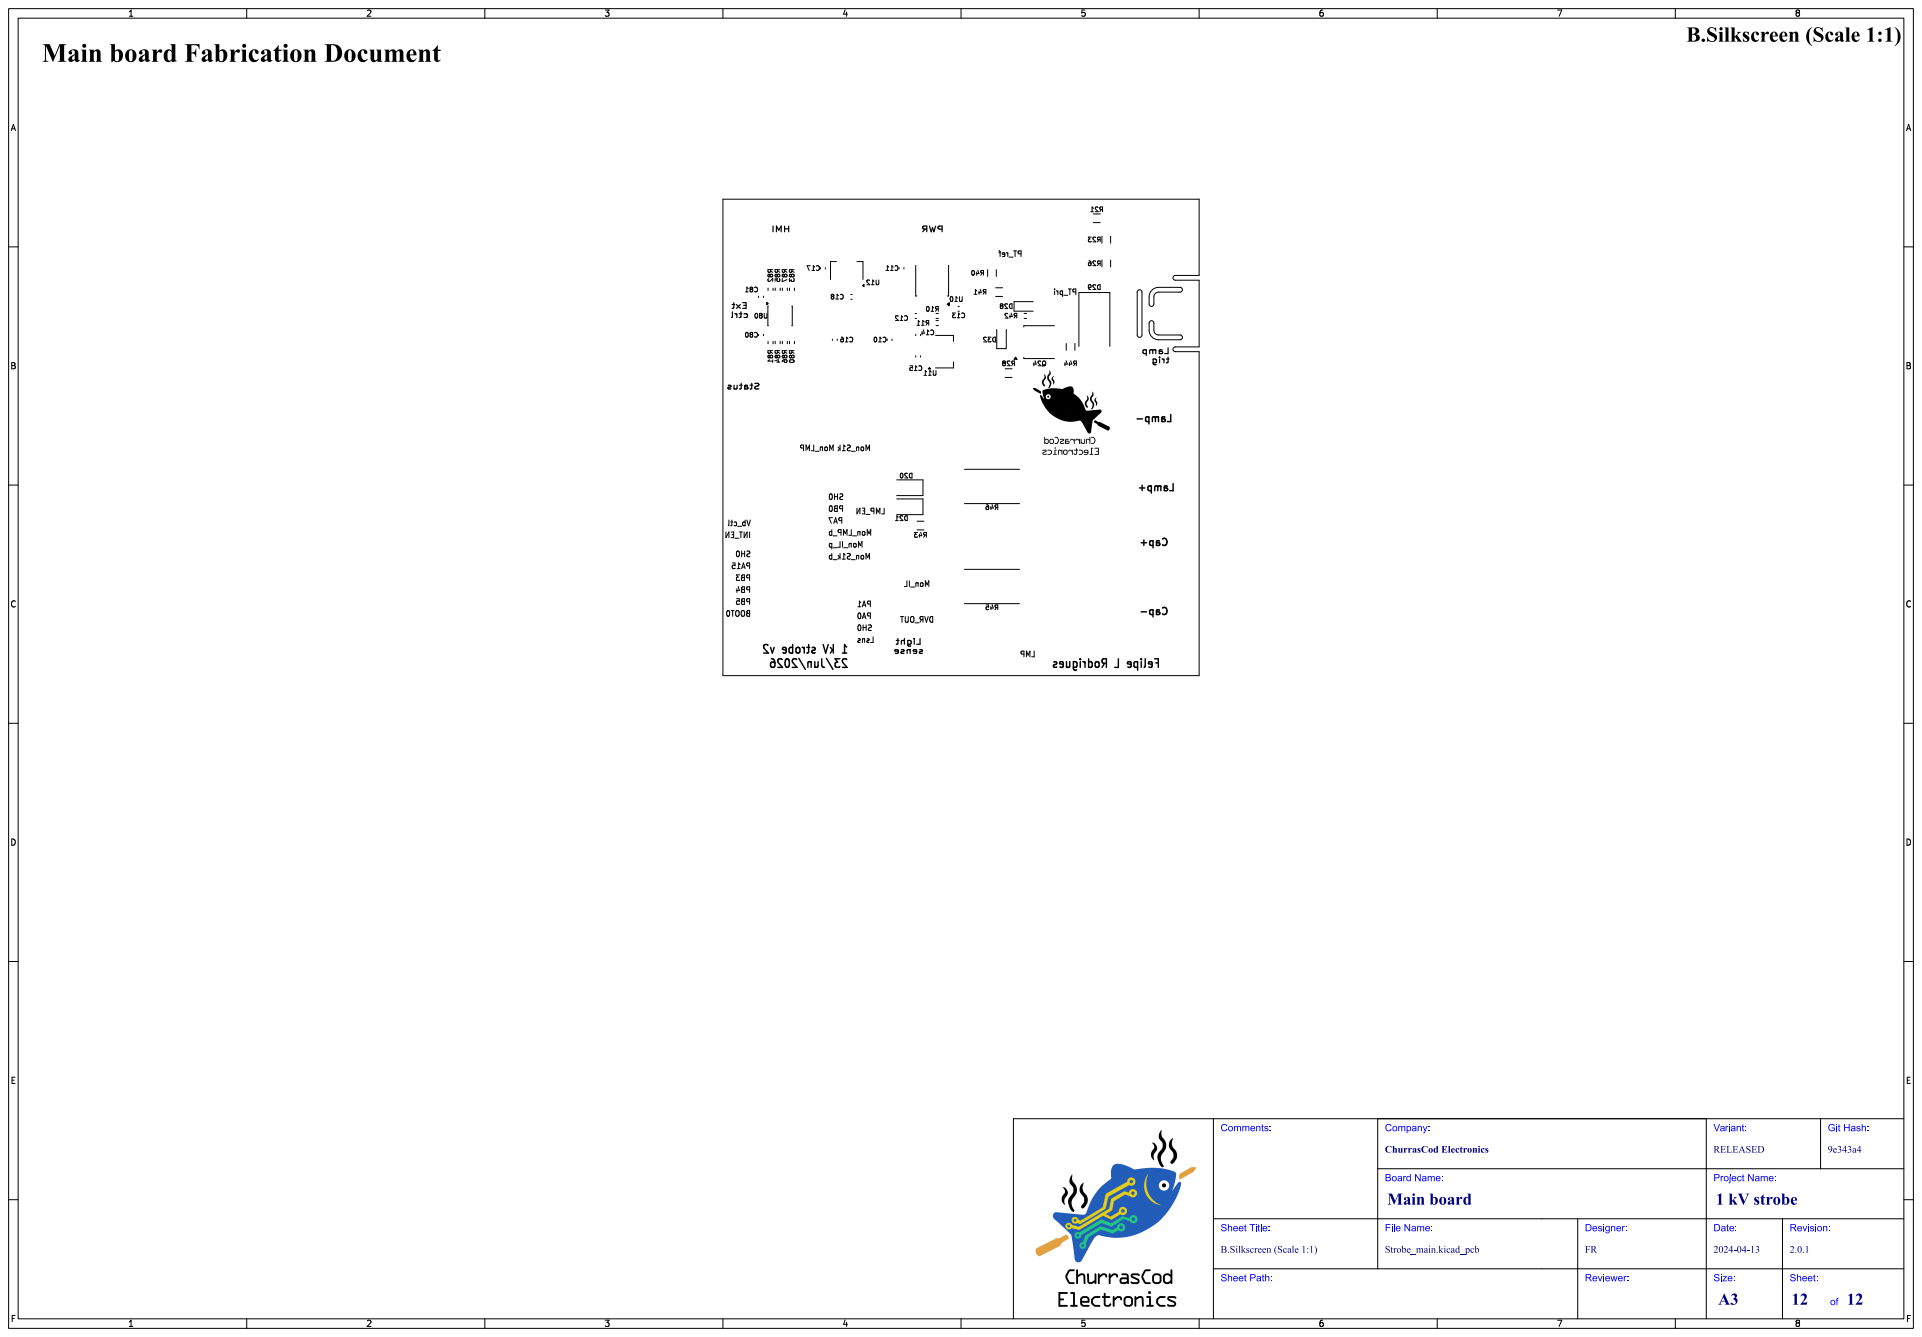
[picture p23: page 12]
