FLRHW/Strobe_main/Manufacturing/Assembly/Strobe_main-assembly.pdf

# Top Assembly (Scale 1:1) Main board Assembly Document


# Bottom Assembly (Scale 1:1) Main board Assembly Document
