FLRHW/Strobe_main/Manufacturing/Fabrication/Strobe_main-fabrication-1.pdf

# Top Fabrication (Scale 1:1) Main board Fabrication Document
