FLRHW/Strobe_main/Manufacturing/Fabrication/Strobe_main-fabrication-11.pdf

# F.Silkscreen (Scale 1:1) Main board Fabrication Document
