FLRHW/Strobe_main/Manufacturing/Fabrication/Strobe_main-fabrication-12.pdf

# B.Silkscreen (Scale 1:1) Main board Fabrication Document
