FLRHW/Strobe_main/Manufacturing/Fabrication/Strobe_main-fabrication-2.pdf

# Bottom Fabrication (Scale 1:1) Main board Fabrication Document
