FLRHW/Strobe_main/Manufacturing/Fabrication/Strobe_main-fabrication-3.pdf

# Drill Drawing L1 - L4 (Scale 1:1) Main board Fabrication Document

Git; Hash:; Comments:; Drill Drawing (L1 - L4); Sheet Path:; Sheet Title:; File Name:; Main board; 1 kV strobe; ChurrasCod Electronics; Company:; RELEASED; Variant:; Board Name:; Strobe_main.kicad_pcb; Designer:; Reviewer:; Project Name:; Date:; Revision:; Size:; Sheet: 3
