FLRHW/Strobe_main/Manufacturing/Fabrication/Strobe_main-fabrication-7.pdf

# In2.Cu (Sig, PWR) (Scale 1:1) Main board Fabrication Document

Git; Hash:; Comments:; Sheet Path:; Sheet Title:; File Name:; Main board; 1 kV strobe; ChurrasCod Electronics; Company:; RELEASED; Variant:; Board Name:; Strobe_main.kicad_pcb; Designer:; Reviewer:; Project Name:; Date:; Revision:; Size:; Sheet: 7

In2.Cu (Sig, PWR) (Scale 1:1)
