FLRHW/Strobe_main/Manufacturing/Fabrication/Strobe_main-fabrication-13.pdf

# F.Silkscreen (Scale 1:1) Main board Fabrication Document

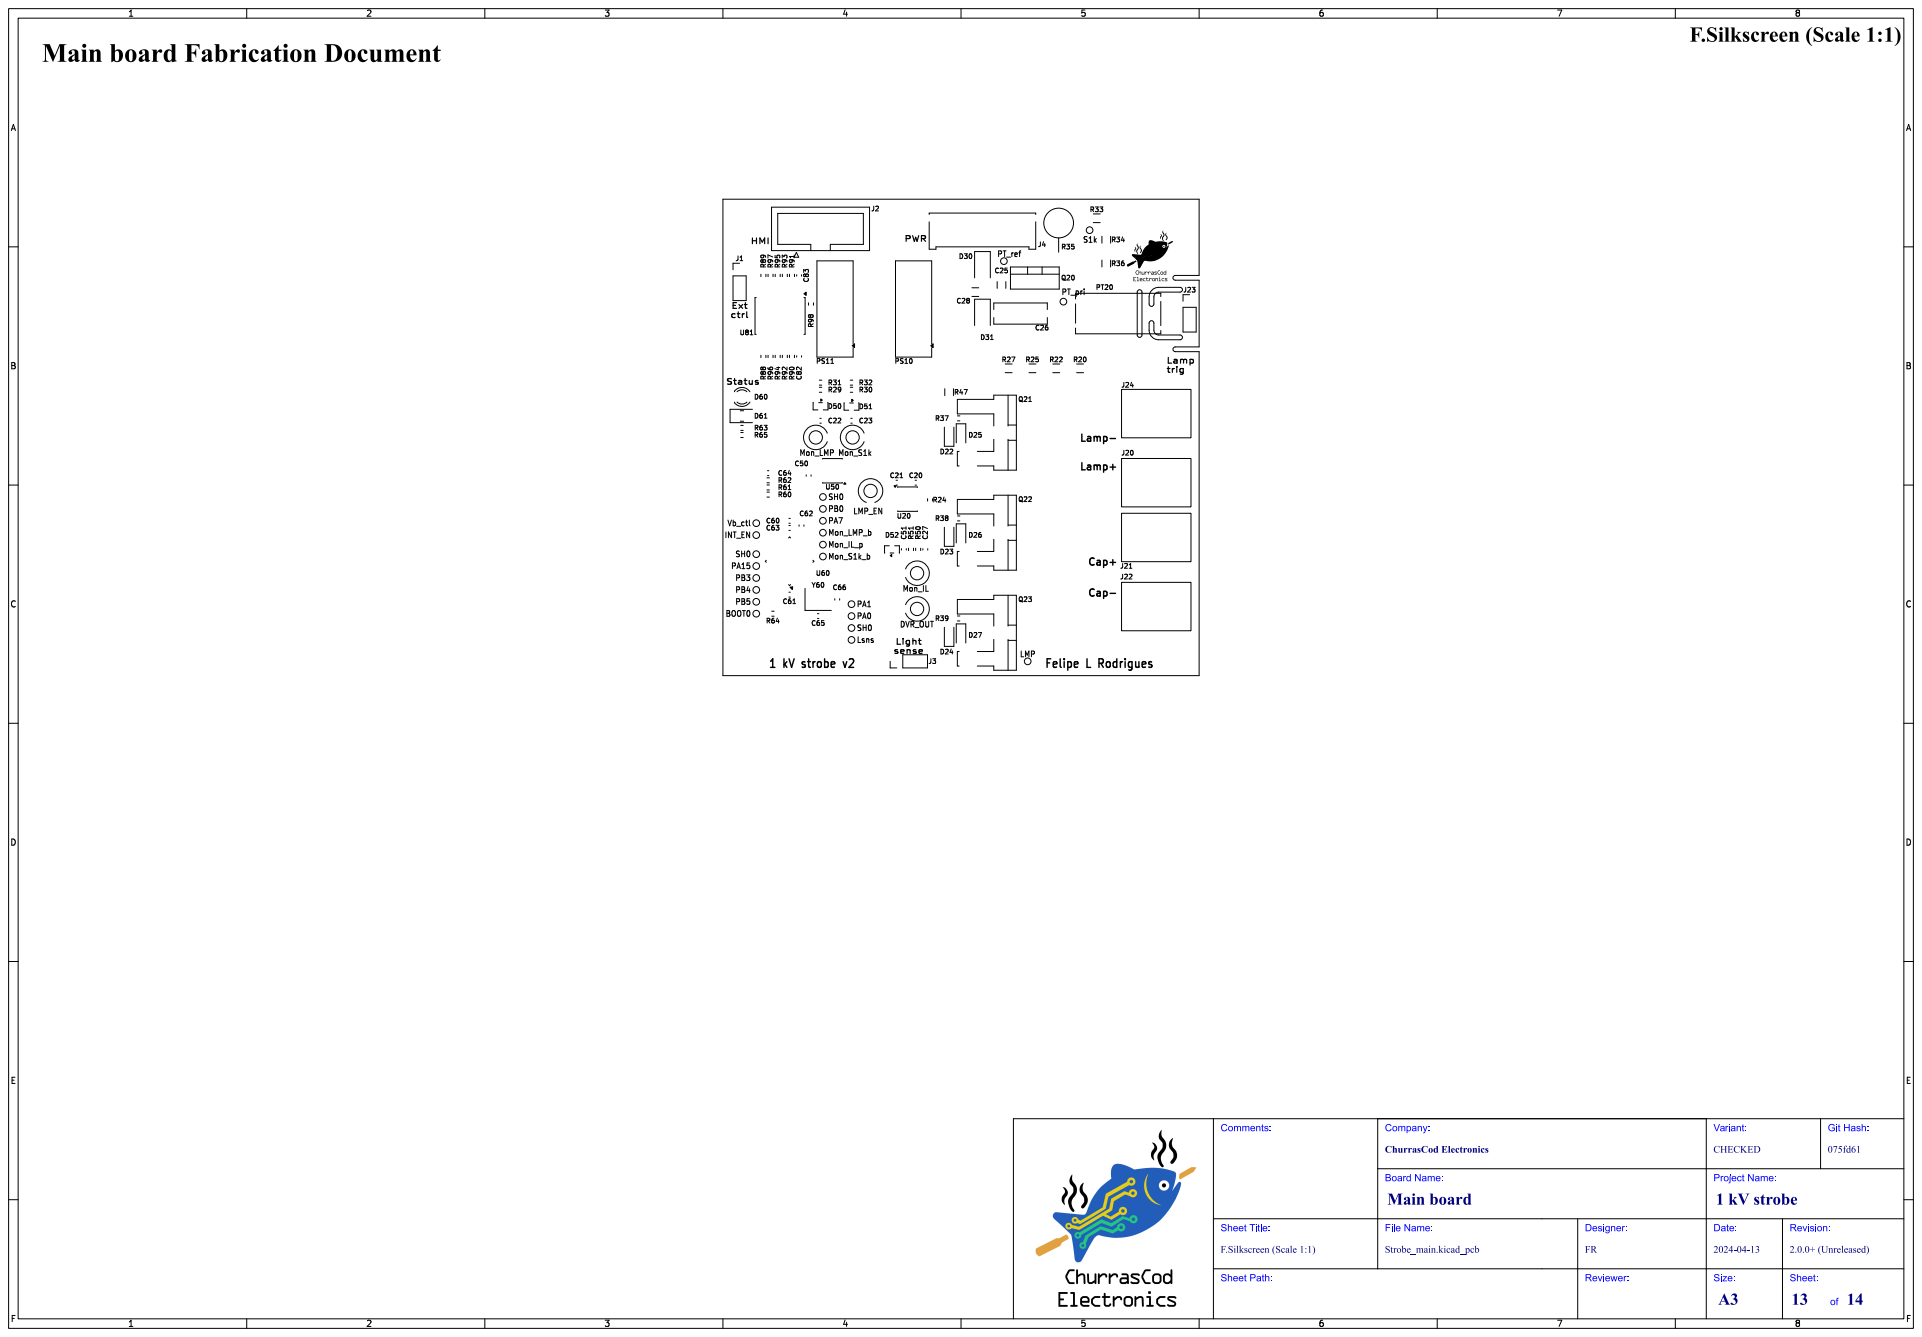
[picture p37: page 1]
