FLRHW/Strobe_main/Manufacturing/Fabrication/Strobe_main-fabrication-14.pdf

# B.Silkscreen (Scale 1:1) Main board Fabrication Document

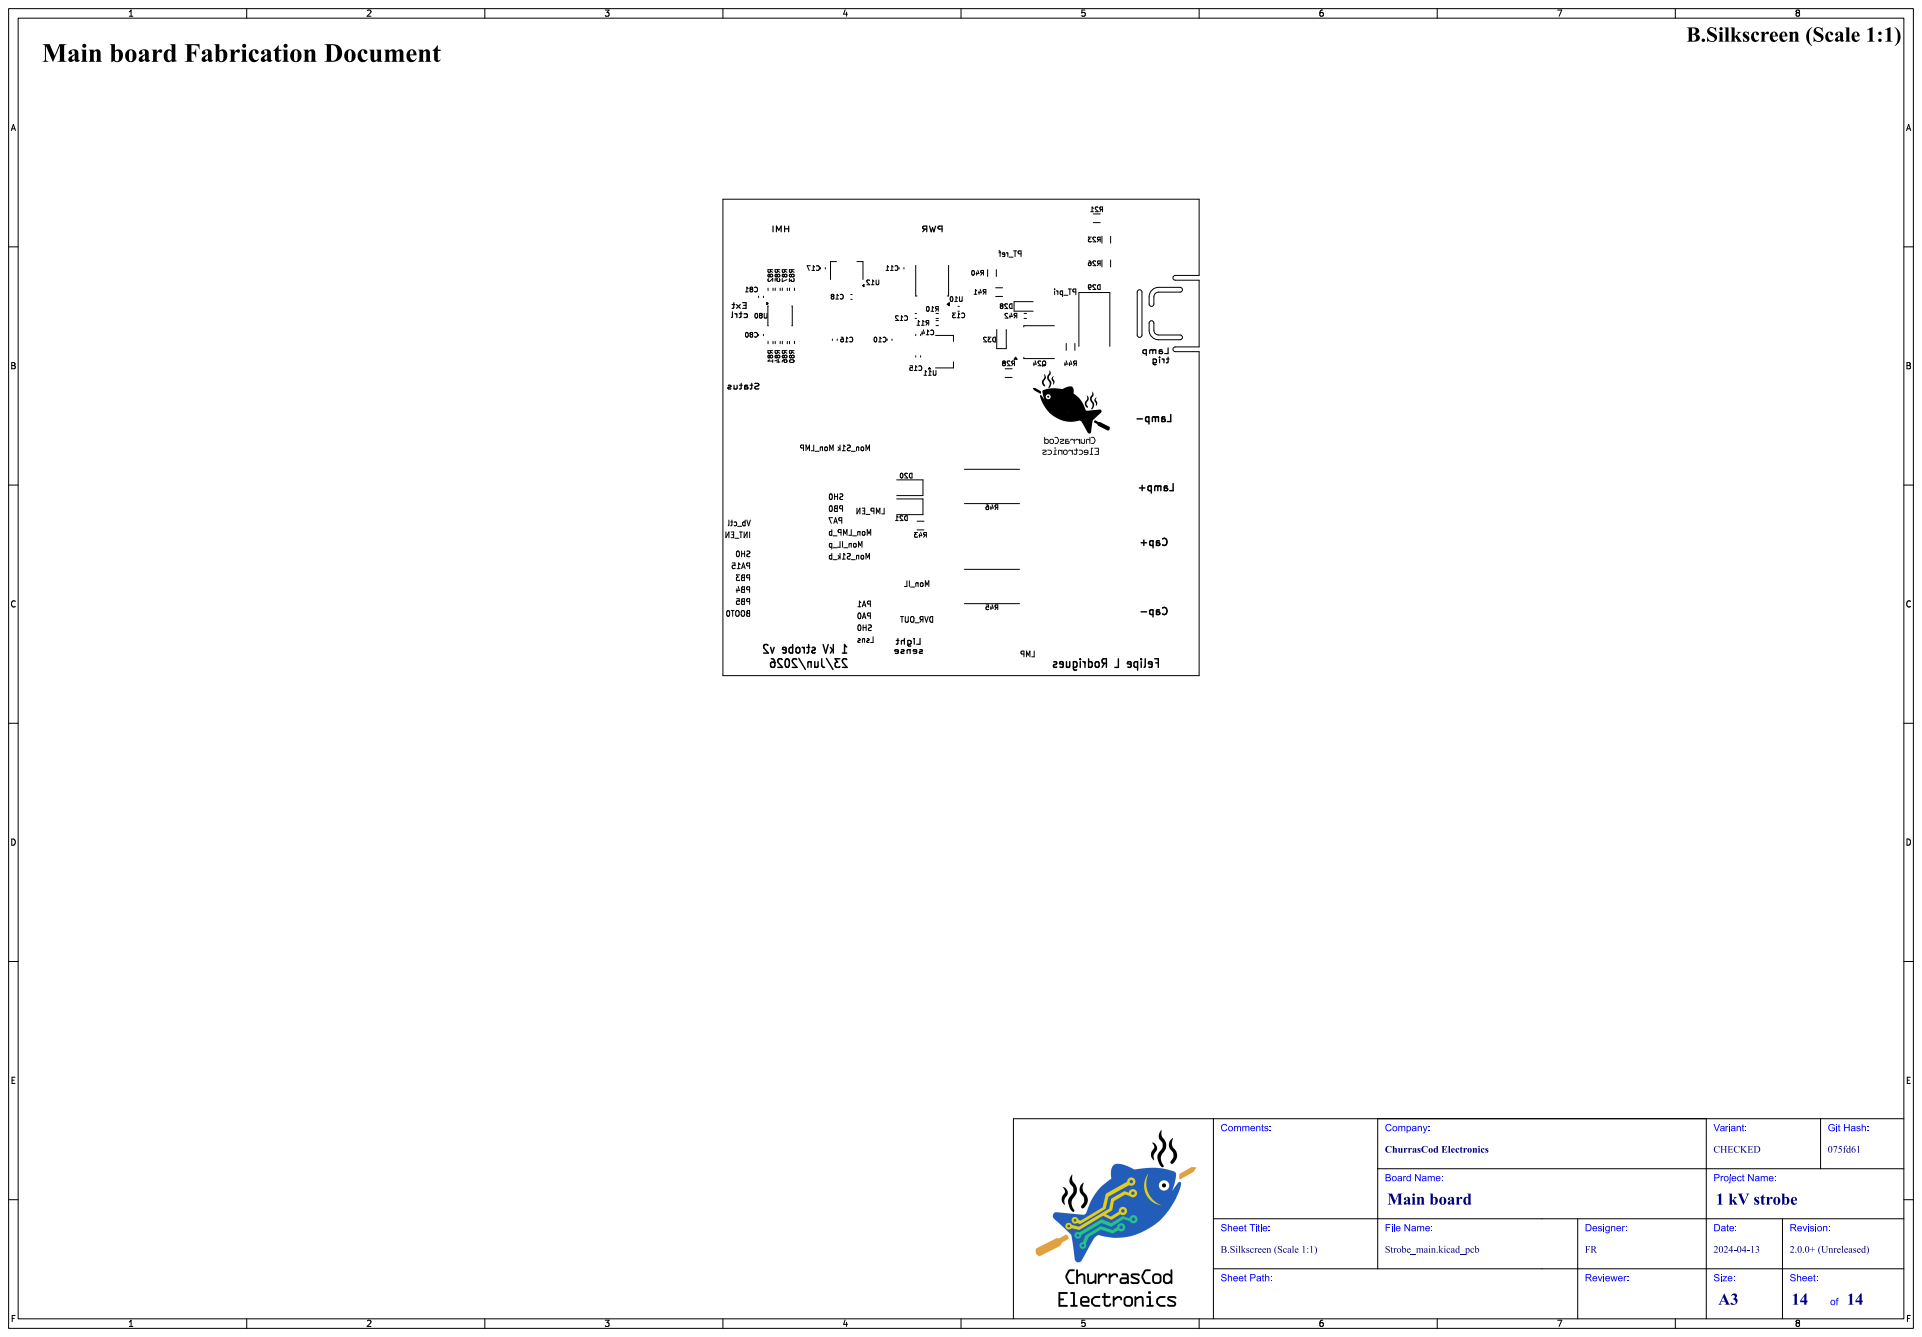
[picture p38: page 1]
