FLRHW/Strobe_main/Manufacturing/Assembly/Strobe_main-assembly-3.pdf

# Bottom Assembly (Scale 1:1) Main board Assembly Document

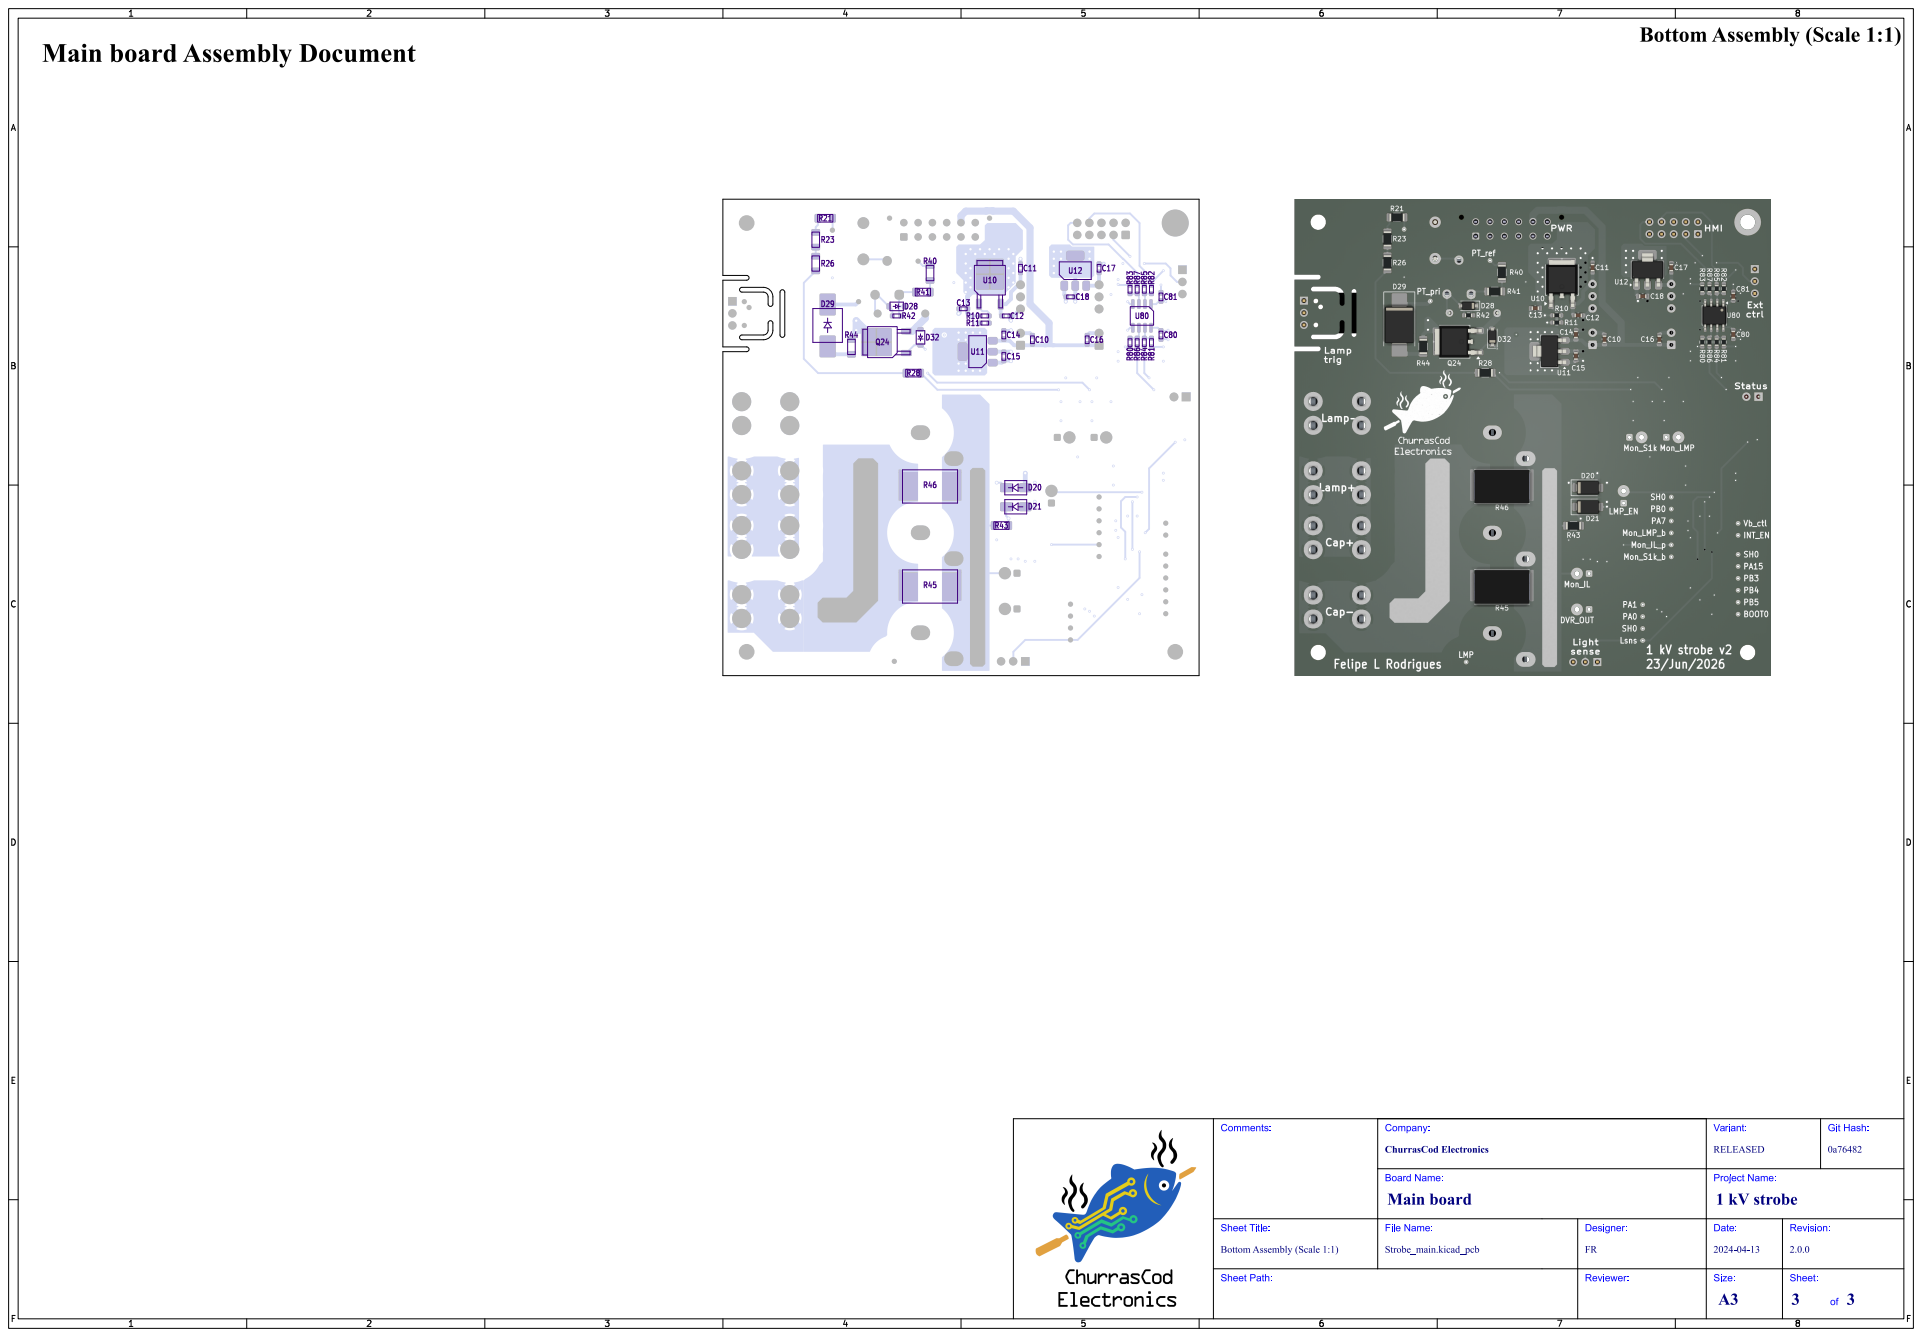
[picture p39: page 1]
