FLRHW/Strobe_main/Manufacturing/Fabrication/Gerbers/Strobe_main-NPTH_drill_map.pdf

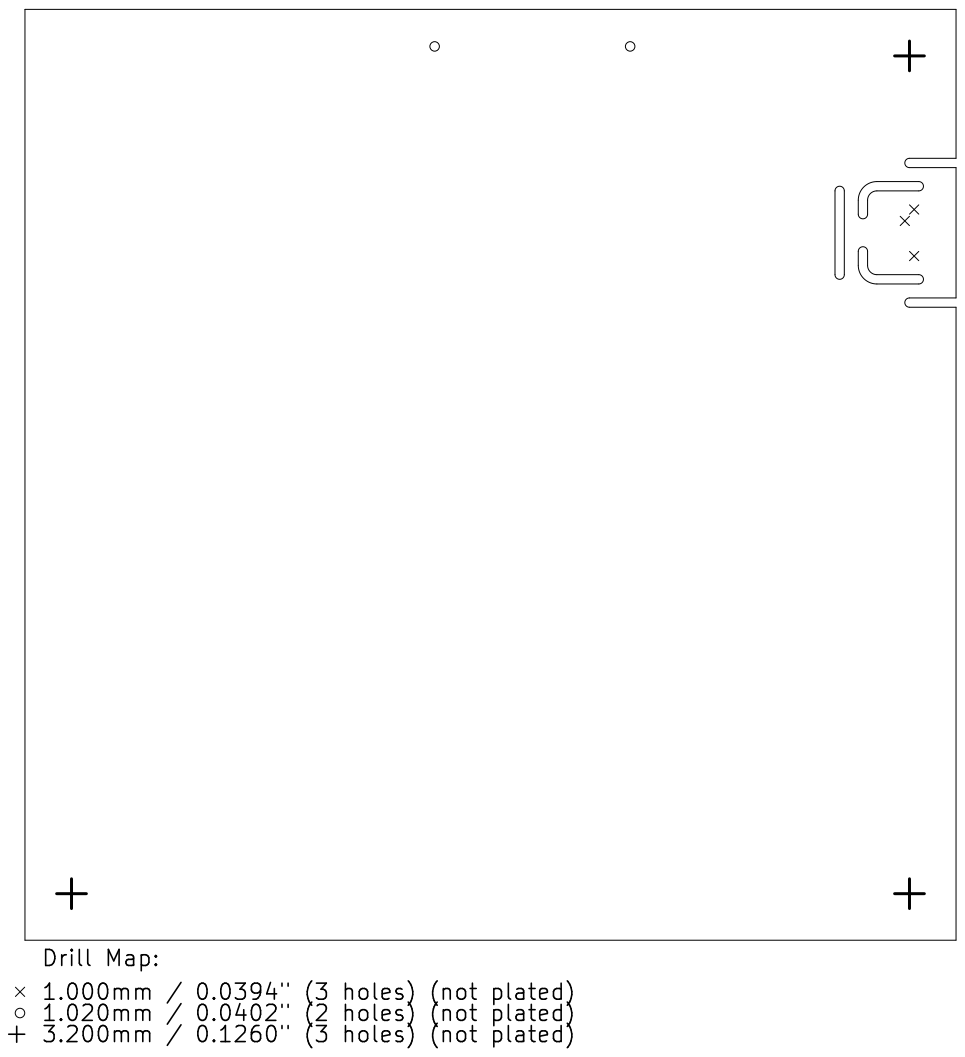
[picture p40: page 1]
