FLRHW/Strobe_main/Manufacturing/Fabrication/Gerbers/Strobe_main-PTH_drill_map.pdf

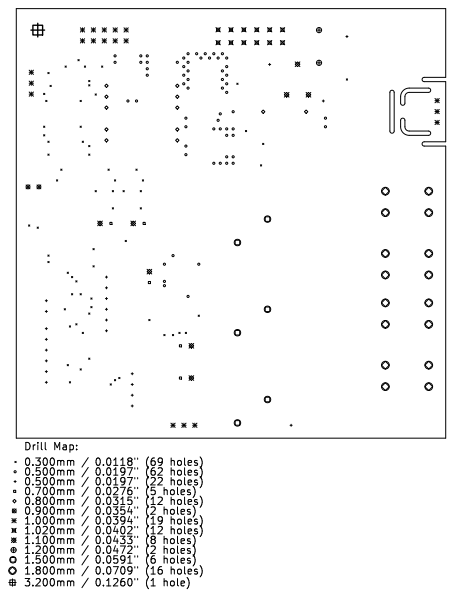
[picture p41: page 1]
