FLRHW/Strobe_main/Computations/sim/Pulse_gen_tr_model_no_IGBT.asc

C1: cap; 47n
C2: cap; 47n
D1: zener; KDZLV150
D2: zener; KDZLV150
D3: zener; MMBZ24VALY
D4: diode; VS-E5TH1512
L1: ind2; 20µ; Rser=0.32
L2: ind2; 18m; Rser=220
M1: nmos; STW11NM80
R1: res; 100k
R2: res; 200k
R3: res; 990k
R4: res; 100k
R5: res; 1Meg
R6: res; 10
R7: res; 2
S1: sw; MYSW
U1: STFW3N150
V1: voltage; PULSE(1000 1000 0 1 1u 1m 1.1)
V2: voltage; PULSE(-1 20 2u 1u 1u 9u 5m)
Named nets: 0, Cap, drain, bus, ref, HV, trig
.model MYSW SW(Ron=1m Roff=100meg vt=0.5 vh=0.1)
.tran 10u
K1 L1 L2 0.9
