FLRHW/Strobe_main/Computations/sim/Ipeak_cond.asc

C1: cap; 4.7n
R1: res; 220
R2: res; 220
V1: voltage; PULSE(0 6.5 10u 1n 1n 20u 40u)
Named nets: 0, Ipeak_meas
.tran 50u
